JCLemme/eprisc-open-computer/software/rom/bios_main.v

rContents[0] = 32'h80000026;
rContents[1] = 32'h43F01FF0;
rContents[2] = 32'h61F00000;
rContents[3] = 32'hD000029E;
rContents[4] = 32'h63F01FF1;
rContents[5] = 32'h41F00000;
rContents[6] = 32'hF0000000;
rContents[7] = 32'hD00002BC;
rContents[8] = 32'h63F01FF1;
rContents[9] = 32'hF0000000;
rContents[10] = 32'h43F01FF2;
rContents[11] = 32'h61F00000;
rContents[12] = 32'h43F01FF3;
rContents[13] = 32'h61F00000;
rContents[14] = 32'hD00003E9;
rContents[15] = 32'h63F01FF4;
rContents[16] = 32'h41F00000;
rContents[17] = 32'h41F00000;
rContents[18] = 32'hF0000000;
rContents[19] = 32'h43F01FF2;
rContents[20] = 32'h61F00000;
rContents[21] = 32'h43F01FF3;
rContents[22] = 32'h61F00000;
rContents[23] = 32'hD0000415;
rContents[24] = 32'h63F01FF4;
rContents[25] = 32'h41F00000;
rContents[26] = 32'h41F00000;
rContents[27] = 32'hF0000000;
rContents[28] = 32'hD0000340;
rContents[29] = 32'h63F01FF5;
rContents[30] = 32'hF0000000;
rContents[31] = 32'h238000FF;
rContents[32] = 32'h3300FFFF;
rContents[33] = 32'h18133001;
rContents[34] = 32'h18E03000;
rContents[35] = 32'h820FFFFE;
rContents[36] = 32'h18422801;
rContents[37] = 32'h800FFFFA;
rContents[38] = 32'h21001100;
rContents[39] = 32'h23000000;
rContents[40] = 32'h800FFFF7;
rContents[41] = 32'hD00001CD;
rContents[42] = 32'h24007FFF;
rContents[43] = 32'h61400000;
rContents[44] = 32'h24000000;
rContents[45] = 32'h61400000;
rContents[46] = 32'hD00001D8;
rContents[47] = 32'h41400000;
rContents[48] = 32'h41400000;
rContents[49] = 32'h24000132;
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
rContents[283] = 32'h48500003;
rContents[284] = 32'h48600004;
rContents[285] = 32'h48700005;
rContents[286] = 32'h61700000;
rContents[287] = 32'h61500000;
rContents[288] = 32'hD000030C;
rContents[289] = 32'h41500000;
rContents[290] = 32'h41700000;
rContents[291] = 32'h18E0F000;
rContents[292] = 32'h82000009;
rContents[293] = 32'h18055001;
rContents[294] = 32'h18077080;
rContents[295] = 32'h18166001;
rContents[296] = 32'h18E06000;
rContents[297] = 32'h820FFFF5;
rContents[298] = 32'hD00003A4;
rContents[299] = 32'h48700005;
rContents[300] = 32'h80700000;
rContents[301] = 32'h240001EE;
rContents[302] = 32'h61400000;
rContents[303] = 32'hD00001FE;
rContents[304] = 32'h41400000;
rContents[305] = 32'h80000496;
rContents[306] = 32'h65705249;
rContents[307] = 32'h53432042;
rContents[308] = 32'h6F6F746C;
rContents[309] = 32'h6F616465;
rContents[310] = 32'h72207633;
rContents[311] = 32'h2E340A0D;
rContents[312] = 32'h636F7079;
rContents[313] = 32'h72696768;
rContents[314] = 32'h74203230;
rContents[315] = 32'h31352D32;
rContents[316] = 32'h30313720;
rContents[317] = 32'h50726F70;
rContents[318] = 32'h6F727469;
rContents[319] = 32'h6F6E616C;
rContents[320] = 32'h204C6162;
rContents[321] = 32'h730A0D0A;
rContents[322] = 32'h0D000000;
rContents[323] = 32'h41747465;
rContents[324] = 32'h6D707469;
rContents[325] = 32'h6E672074;
rContents[326] = 32'h6F206D6F;
rContents[327] = 32'h756E7420;
rContents[328] = 32'h53442063;
rContents[329] = 32'h61726420;
rContents[330] = 32'h696E2073;
rContents[331] = 32'h6C6F7420;
rContents[332] = 32'h412E2E2E;
rContents[333] = 32'h0A0D0000;
rContents[334] = 32'h41747465;
rContents[335] = 32'h6D707469;
rContents[336] = 32'h6E672074;
rContents[337] = 32'h6F206D6F;
rContents[338] = 32'h756E7420;
rContents[339] = 32'h53442063;
rContents[340] = 32'h61726420;
rContents[341] = 32'h696E2073;
rContents[342] = 32'h6C6F7420;
rContents[343] = 32'h422E2E2E;
rContents[344] = 32'h0A0D0000;
rContents[345] = 32'h20205344;
rContents[346] = 32'h20636172;
rContents[347] = 32'h64206D6F;
rContents[348] = 32'h756E7465;
rContents[349] = 32'h64207375;
rContents[350] = 32'h63636573;
rContents[351] = 32'h7366756C;
rContents[352] = 32'h6C792E0A;
rContents[353] = 32'h0D0A0D00;
rContents[354] = 32'h20204572;
rContents[355] = 32'h726F7220;
rContents[356] = 32'h6D6F756E;
rContents[357] = 32'h74696E67;
rContents[358] = 32'h20534420;
rContents[359] = 32'h63617264;
rContents[360] = 32'h2E0A0D0A;
rContents[361] = 32'h0D000000;
rContents[362] = 32'h46657463;
rContents[363] = 32'h68696E67;
rContents[364] = 32'h20646973;
rContents[365] = 32'h6B20696E;
rContents[366] = 32'h666F2E2E;
rContents[367] = 32'h2E0A0D00;
rContents[368] = 32'h20204469;
rContents[369] = 32'h736B2061;
rContents[370] = 32'h70706561;
rContents[371] = 32'h72732074;
rContents[372] = 32'h6F206265;
rContents[373] = 32'h20636F72;
rContents[374] = 32'h72757074;
rContents[375] = 32'h2E0A0D0A;
rContents[376] = 32'h0D000000;
rContents[377] = 32'h2020466F;
rContents[378] = 32'h756E6420;
rContents[379] = 32'h6469736B;
rContents[380] = 32'h20270000;
rContents[381] = 32'h27206174;
rContents[382] = 32'h20626C6F;
rContents[383] = 32'h636B2030;
rContents[384] = 32'h2E0A0D00;
rContents[385] = 32'h20204469;
rContents[386] = 32'h736B2061;
rContents[387] = 32'h70706561;
rContents[388] = 32'h72732074;
rContents[389] = 32'h6F206265;
rContents[390] = 32'h20656D70;
rContents[391] = 32'h74792E0A;
rContents[392] = 32'h0D0A0D00;
rContents[393] = 32'h2020466F;
rContents[394] = 32'h756E6420;
rContents[395] = 32'h00000000;
rContents[396] = 32'h20656E74;
rContents[397] = 32'h72696573;
rContents[398] = 32'h206F6E20;
rContents[399] = 32'h6469736B;
rContents[400] = 32'h2E0A0D0A;
rContents[401] = 32'h0D000000;
rContents[402] = 32'h41766169;
rContents[403] = 32'h6C61626C;
rContents[404] = 32'h6520656E;
rContents[405] = 32'h74726965;
rContents[406] = 32'h733A0A0D;
rContents[407] = 32'h00000000;
rContents[408] = 32'h3A20456E;
rContents[409] = 32'h74727920;
rContents[410] = 32'h27000000;
rContents[411] = 32'h273A2073;
rContents[412] = 32'h74617274;
rContents[413] = 32'h20000000;
rContents[414] = 32'h2C206C65;
rContents[415] = 32'h6E677468;
rContents[416] = 32'h20000000;
rContents[417] = 32'h2C206C6F;
rContents[418] = 32'h61642000;
rContents[419] = 32'h53656C65;
rContents[420] = 32'h63742061;
rContents[421] = 32'h6E20656E;
rContents[422] = 32'h74727920;
rContents[423] = 32'h746F2065;
rContents[424] = 32'h78656375;
rContents[425] = 32'h74652C20;
rContents[426] = 32'h6F722074;
rContents[427] = 32'h79706520;
rContents[428] = 32'h274D2720;
rContents[429] = 32'h746F2065;
rContents[430] = 32'h6E746572;
rContents[431] = 32'h20746865;
rContents[432] = 32'h206D6F6E;
rContents[433] = 32'h69746F72;
rContents[434] = 32'h3A200000;
rContents[435] = 32'h20204C6F;
rContents[436] = 32'h6164696E;
rContents[437] = 32'h6720656E;
rContents[438] = 32'h7472792E;
rContents[439] = 32'h2E2E0A0D;
rContents[440] = 32'h0A0D0000;
rContents[441] = 32'h53746172;
rContents[442] = 32'h74696E67;
rContents[443] = 32'h20504F53;
rContents[444] = 32'h54732E2E;
rContents[445] = 32'h2E0A0D00;
rContents[446] = 32'h20204D65;
rContents[447] = 32'h6D6F7279;
rContents[448] = 32'h20202020;
rContents[449] = 32'h20202020;
rContents[450] = 32'h20200000;
rContents[451] = 32'h20205541;
rContents[452] = 32'h52542020;
rContents[453] = 32'h20202020;
rContents[454] = 32'h20202020;
rContents[455] = 32'h20200000;
rContents[456] = 32'h20205350;
rContents[457] = 32'h49202020;
rContents[458] = 32'h20202020;
rContents[459] = 32'h20202020;
rContents[460] = 32'h20200000;
rContents[461] = 32'h20207379;
rContents[462] = 32'h73582042;
rContents[463] = 32'h75732020;
rContents[464] = 32'h20202020;
rContents[465] = 32'h20200000;
rContents[466] = 32'h2020492F;
rContents[467] = 32'h4F20436F;
rContents[468] = 32'h6E74726F;
rContents[469] = 32'h6C6C6572;
rContents[470] = 32'h20200000;
rContents[471] = 32'h4F4B0A0D;
rContents[472] = 32'h00000000;
rContents[473] = 32'h4641494C;
rContents[474] = 32'h0A0D0000;
rContents[475] = 32'h2020504F;
rContents[476] = 32'h53542073;
rContents[477] = 32'h75636365;
rContents[478] = 32'h73736675;
rContents[479] = 32'h6C2E0A0D;
rContents[480] = 32'h0A0D0000;
rContents[481] = 32'h2020504F;
rContents[482] = 32'h53542075;
rContents[483] = 32'h6E737563;
rContents[484] = 32'h63657373;
rContents[485] = 32'h66756C2E;
rContents[486] = 32'h0A0D0A0D;
rContents[487] = 32'h00000000;
rContents[488] = 32'h2020504F;
rContents[489] = 32'h53547320;
rContents[490] = 32'h636F6D70;
rContents[491] = 32'h6C657465;
rContents[492] = 32'h2E0A0D0A;
rContents[493] = 32'h0D000000;
rContents[494] = 32'h456E7465;
rContents[495] = 32'h72696E67;
rContents[496] = 32'h206D6F6E;
rContents[497] = 32'h69746F72;
rContents[498] = 32'h2E2E2E0A;
rContents[499] = 32'h0D0A0D00;
rContents[500] = 32'h0A0D0000;
rContents[501] = 32'h20200000;
rContents[502] = 32'h61C00000;
rContents[503] = 32'h2C002000;
rContents[504] = 32'h2F010001;
rContents[505] = 32'h6CF00000;
rContents[506] = 32'h04000000;
rContents[507] = 32'h04000000;
rContents[508] = 32'h04000000;
rContents[509] = 32'h04000000;
rContents[510] = 32'h4CF00000;
rContents[511] = 32'h18F0F001;
rContents[512] = 32'h820FFFFE;
rContents[513] = 32'h4CF00000;
rContents[514] = 32'h18F0F002;
rContents[515] = 32'h820FFFFE;
rContents[516] = 32'h41C00000;
rContents[517] = 32'hF0000000;
rContents[518] = 32'h61E00000;
rContents[519] = 32'h61D00000;
rContents[520] = 32'h61C00000;
rContents[521] = 32'h18111004;
rContents[522] = 32'h2C002000;
rContents[523] = 32'h41D00000;
rContents[524] = 32'h41E00000;
rContents[525] = 32'h18011006;
rContents[526] = 32'h2F600008;
rContents[527] = 32'h103FFE00;
rContents[528] = 32'h186FF010;
rContents[529] = 32'h103FFD00;
rContents[530] = 32'h6CF00001;
rContents[531] = 32'h2F010005;
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
rContents[859] = 32'hF0000000;
rContents[860] = 32'h61C00000;
rContents[861] = 32'h61D00000;
rContents[862] = 32'h61E00000;
rContents[863] = 32'h2C000000;
rContents[864] = 32'h61C00000;
rContents[865] = 32'hD00FFF2C;
rContents[866] = 32'h41C00000;
rContents[867] = 32'h2C00000B;
rContents[868] = 32'hD00FFF5F;
rContents[869] = 32'h181CC001;
rContents[870] = 32'h18E0C000;
rContents[871] = 32'h820FFFFD;
rContents[872] = 32'h2C000001;
rContents[873] = 32'h61C00000;
rContents[874] = 32'hD00FFF23;
rContents[875] = 32'h41C00000;
rContents[876] = 32'h2C000000;
rContents[877] = 32'h61C00000;
rContents[878] = 32'h2C000000;
rContents[879] = 32'h61C00000;
rContents[880] = 32'h2D000001;
rContents[881] = 32'h186DD000;
rContents[882] = 32'h2E000000;
rContents[883] = 32'hD0000084;
rContents[884] = 32'h10E0FD00;
rContents[885] = 32'h81000005;
rContents[886] = 32'h180EE001;
rContents[887] = 32'h18E0E402;
rContents[888] = 32'h8100006E;
rContents[889] = 32'h800FFFFA;
rContents[890] = 32'h41C00000;
rContents[891] = 32'h41C00000;
rContents[892] = 32'h2C000008;
rContents[893] = 32'h61C00000;
rContents[894] = 32'h2C0001AA;
rContents[895] = 32'h61C00000;
rContents[896] = 32'hD0000077;
rContents[897] = 32'h41C00000;
rContents[898] = 32'h41C00000;
rContents[899] = 32'h2D000001;
rContents[900] = 32'h186DD002;
rContents[901] = 32'h10F0FD00;
rContents[902] = 32'h8200000C;
rContents[903] = 32'hD00FFF3C;
rContents[904] = 32'hD00FFF3B;
rContents[905] = 32'hD00FFF3A;
rContents[906] = 32'h18F0F001;
rContents[907] = 32'h8100005D;
rContents[908] = 32'hD00FFF37;
rContents[909] = 32'h18E0F0AA;
rContents[910] = 32'h8200005A;
rContents[911] = 32'h2E000001;
rContents[912] = 32'h186EE001;
rContents[913] = 32'h80000014;
rContents[914] = 32'h2C000037;
rContents[915] = 32'h61C00000;
rContents[916] = 32'h2C000000;
rContents[917] = 32'h61C00000;
rContents[918] = 32'hD0000061;
rContents[919] = 32'h41C00000;
rContents[920] = 32'h41C00000;
rContents[921] = 32'h2C000029;
rContents[922] = 32'h61C00000;
rContents[923] = 32'h2C000000;
rContents[924] = 32'h61C00000;
rContents[925] = 32'hD000005A;
rContents[926] = 32'h41C00000;
rContents[927] = 32'h41C00000;
rContents[928] = 32'h2E000000;
rContents[929] = 32'h10E0FD00;
rContents[930] = 32'h82000003;
rContents[931] = 32'h2E000001;
rContents[932] = 32'h186EE000;
rContents[933] = 32'h2D000000;
rContents[934] = 32'h18F0E003;
rContents[935] = 32'h81000013;
rContents[936] = 32'h2C000037;
rContents[937] = 32'h61C00000;
rContents[938] = 32'h2C000000;
rContents[939] = 32'h61C00000;
rContents[940] = 32'hD000004B;
rContents[941] = 32'h41C00000;
rContents[942] = 32'h41C00000;
rContents[943] = 32'h2C000029;
rContents[944] = 32'h61C00000;
rContents[945] = 32'h2C000000;
rContents[946] = 32'h18F0E002;
rContents[947] = 32'h81000002;
rContents[948] = 32'h2C804000;
rContents[949] = 32'h61C00000;
rContents[950] = 32'hD0000041;
rContents[951] = 32'h41C00000;
rContents[952] = 32'h41C00000;
rContents[953] = 32'h80000008;
rContents[954] = 32'h2C000029;
rContents[955] = 32'h61C00000;
rContents[956] = 32'h2C000000;
rContents[957] = 32'h61C00000;
rContents[958] = 32'hD0000039;
rContents[959] = 32'h41C00000;
rContents[960] = 32'h41C00000;
rContents[961] = 32'h18F0F001;
rContents[962] = 32'h81000005;
rContents[963] = 32'h180DD001;
rContents[964] = 32'h18E0D480;
rContents[965] = 32'h81000023;
rContents[966] = 32'h800FFFE0;
rContents[967] = 32'h18F0E002;
rContents[968] = 32'h81000013;
rContents[969] = 32'h2C00003A;
rContents[970] = 32'h61C00000;
rContents[971] = 32'h2C000000;
rContents[972] = 32'h61C00000;
rContents[973] = 32'hD000002A;
rContents[974] = 32'h41C00000;
rContents[975] = 32'h41C00000;
rContents[976] = 32'h18E0F000;
rContents[977] = 32'h82000017;
rContents[978] = 32'hD00FFEF1;
rContents[979] = 32'h18F0F040;
rContents[980] = 32'h81000004;
rContents[981] = 32'h2C000001;
rContents[982] = 32'h186CC002;
rContents[983] = 32'h103EEC00;
rContents[984] = 32'hD00FFEEB;
rContents[985] = 32'hD00FFEEA;
rContents[986] = 32'hD00FFEE9;
rContents[987] = 32'h2C000010;
rContents[988] = 32'h61C00000;
rContents[989] = 32'h2C000200;
rContents[990] = 32'h61C00000;
rContents[991] = 32'hD0000018;
rContents[992] = 32'h41C00000;
rContents[993] = 32'h41C00000;
rContents[994] = 32'h18E0F000;
rContents[995] = 32'h82000005;
rContents[996] = 32'h8000000A;
rContents[997] = 32'hD00001B4;
rContents[998] = 32'h41C00000;
rContents[999] = 32'h41C00000;
rContents[1000] = 32'h2C000000;
rContents[1001] = 32'h61C00000;
rContents[1002] = 32'hD00FFEA3;
rContents[1003] = 32'h41C00000;
rContents[1004] = 32'h2F0000FF;
rContents[1005] = 32'h80000006;
rContents[1006] = 32'h2C000000;
rContents[1007] = 32'h61C00000;
rContents[1008] = 32'hD00FFE9D;
rContents[1009] = 32'h41C00000;
rContents[1010] = 32'h08FE0000;
rContents[1011] = 32'h41E00000;
rContents[1012] = 32'h41D00000;
rContents[1013] = 32'h41C00000;
rContents[1014] = 32'hF0000000;
rContents[1015] = 32'h61C00000;
rContents[1016] = 32'h61D00000;
rContents[1017] = 32'h18111003;
rContents[1018] = 32'h41D00000;
rContents[1019] = 32'h41C00000;
rContents[1020] = 32'h18011005;
rContents[1021] = 32'hD00FFEC6;
rContents[1022] = 32'h183CC040;
rContents[1023] = 32'h61C00000;
rContents[1024] = 32'hD00FFEA1;
rContents[1025] = 32'h41C00000;
rContents[1026] = 32'h61C00000;
rContents[1027] = 32'h08CD0000;
rContents[1028] = 32'h18DDCCFF;
rContents[1029] = 32'h61D00000;
rContents[1030] = 32'hD00FFE9B;
rContents[1031] = 32'h41D00000;
rContents[1032] = 32'h18DDC8FF;
rContents[1033] = 32'h61D00000;
rContents[1034] = 32'hD00FFE97;
rContents[1035] = 32'h41D00000;
rContents[1036] = 32'h18DDC4FF;
rContents[1037] = 32'h61D00000;
rContents[1038] = 32'hD00FFE93;
rContents[1039] = 32'h41D00000;
rContents[1040] = 32'h18DDC0FF;
rContents[1041] = 32'h61D00000;
rContents[1042] = 32'hD00FFE8F;
rContents[1043] = 32'h41D00000;
rContents[1044] = 32'h41C00000;
rContents[1045] = 32'h18E0C040;
rContents[1046] = 32'h82000003;
rContents[1047] = 32'h2D000095;
rContents[1048] = 32'h80000006;
rContents[1049] = 32'h18E0C048;
rContents[1050] = 32'h82000003;
rContents[1051] = 32'h2D000087;
rContents[1052] = 32'h80000002;
rContents[1053] = 32'h2D0000FF;
rContents[1054] = 32'h61D00000;
rContents[1055] = 32'hD00FFE82;
rContents[1056] = 32'h41D00000;
rContents[1057] = 32'h2D00000A;
rContents[1058] = 32'hD00FFEA1;
rContents[1059] = 32'h18E0F0FF;
rContents[1060] = 32'h82000005;
rContents[1061] = 32'h181DD001;
rContents[1062] = 32'h18E0D000;
rContents[1063] = 32'h81000002;
rContents[1064] = 32'h800FFFFA;
rContents[1065] = 32'h41D00000;
rContents[1066] = 32'h41C00000;
rContents[1067] = 32'hF0000000;
rContents[1068] = 32'h61C00000;
rContents[1069] = 32'h61D00000;
rContents[1070] = 32'h61E00000;
rContents[1071] = 32'h18111004;
rContents[1072] = 32'h41D00000;
rContents[1073] = 32'h41C00000;
rContents[1074] = 32'h18011006;
rContents[1075] = 32'h2F000001;
rContents[1076] = 32'h61F00000;
rContents[1077] = 32'hD00FFE58;
rContents[1078] = 32'h41F00000;
rContents[1079] = 32'h186DD009;
rContents[1080] = 32'h2F000011;
rContents[1081] = 32'h61F00000;
rContents[1082] = 32'h61D00000;
rContents[1083] = 32'hD00FFFBC;
rContents[1084] = 32'h18111002;
rContents[1085] = 32'h18E0F000;
rContents[1086] = 32'h82000023;
rContents[1087] = 32'hD00FFE84;
rContents[1088] = 32'h18E0F0FE;
rContents[1089] = 32'h820FFFFE;
rContents[1090] = 32'h2E000080;
rContents[1091] = 32'h2D000000;
rContents[1092] = 32'hD00FFE7F;
rContents[1093] = 32'h186DF018;
rContents[1094] = 32'hD00FFE7D;
rContents[1095] = 32'h186FF010;
rContents[1096] = 32'h103DDF00;
rContents[1097] = 32'hD00FFE7A;
rContents[1098] = 32'h186FF008;
rContents[1099] = 32'h103DDF00;
rContents[1100] = 32'hD00FFE77;
rContents[1101] = 32'h103DDF00;
rContents[1102] = 32'h6CD00000;
rContents[1103] = 32'h180CC001;
rContents[1104] = 32'h181EE001;
rContents[1105] = 32'h18E0E000;
rContents[1106] = 32'h820FFFF2;
rContents[1107] = 32'hD00FFE70;
rContents[1108] = 32'hD00FFE6F;
rContents[1109] = 32'h2F000000;
rContents[1110] = 32'h61F00000;
rContents[1111] = 32'hD00FFE36;
rContents[1112] = 32'h41F00000;
rContents[1113] = 32'hD00FFE6A;
rContents[1114] = 32'hD00FFE69;
rContents[1115] = 32'hD00FFE68;
rContents[1116] = 32'hD00FFE67;
rContents[1117] = 32'hD00FFE66;
rContents[1118] = 32'hD00FFE65;
rContents[1119] = 32'h2F000000;
rContents[1120] = 32'h80000009;
rContents[1121] = 32'h61F00000;
rContents[1122] = 32'hD00FFE7F;
rContents[1123] = 32'h41F00000;
rContents[1124] = 32'h2F000000;
rContents[1125] = 32'h61F00000;
rContents[1126] = 32'hD00FFE27;
rContents[1127] = 32'h41F00000;
rContents[1128] = 32'h2F0000FF;
rContents[1129] = 32'h41E00000;
rContents[1130] = 32'h41D00000;
rContents[1131] = 32'h41C00000;
rContents[1132] = 32'hF0000000;
rContents[1133] = 32'h61C00000;
rContents[1134] = 32'h61D00000;
rContents[1135] = 32'h61E00000;
rContents[1136] = 32'h18111004;
rContents[1137] = 32'h41D00000;
rContents[1138] = 32'h41C00000;
rContents[1139] = 32'h18011006;
rContents[1140] = 32'h2F000001;
rContents[1141] = 32'h61F00000;
rContents[1142] = 32'hD00FFE17;
rContents[1143] = 32'h41F00000;
rContents[1144] = 32'h2F000018;
rContents[1145] = 32'h61F00000;
rContents[1146] = 32'h61D00000;
rContents[1147] = 32'hD00FFF7C;
rContents[1148] = 32'h18111002;
rContents[1149] = 32'h18E0F000;
rContents[1150] = 32'h8200002E;
rContents[1151] = 32'h2F0000FE;
rContents[1152] = 32'h61F00000;
rContents[1153] = 32'hD00FFE20;
rContents[1154] = 32'h41F00000;
rContents[1155] = 32'h2E000080;
rContents[1156] = 32'h4CD00000;
rContents[1157] = 32'h61C00000;
rContents[1158] = 32'h182CDCFF;
rContents[1159] = 32'h188DD018;
rContents[1160] = 32'h61D00000;
rContents[1161] = 32'hD00FFE18;
rContents[1162] = 32'h41D00000;
rContents[1163] = 32'h182CD8FF;
rContents[1164] = 32'h188DD010;
rContents[1165] = 32'h61D00000;
rContents[1166] = 32'hD00FFE13;
rContents[1167] = 32'h41D00000;
rContents[1168] = 32'h182CD4FF;
rContents[1169] = 32'h188DD008;
rContents[1170] = 32'h61D00000;
rContents[1171] = 32'hD00FFE0E;
rContents[1172] = 32'h41D00000;
rContents[1173] = 32'h182CD0FF;
rContents[1174] = 32'h61D00000;
rContents[1175] = 32'hD00FFE0A;
rContents[1176] = 32'h41D00000;
rContents[1177] = 32'h41C00000;
rContents[1178] = 32'h180CC001;
rContents[1179] = 32'h181EE001;
rContents[1180] = 32'h18E0E000;
rContents[1181] = 32'h820FFFE7;
rContents[1182] = 32'h2F0000FF;
rContents[1183] = 32'h61F00000;
rContents[1184] = 32'hD00FFE01;
rContents[1185] = 32'hD00FFE00;
rContents[1186] = 32'h41F00000;
rContents[1187] = 32'hD00FFE20;
rContents[1188] = 32'h18E0F0FF;
rContents[1189] = 32'h820FFFFE;
rContents[1190] = 32'h2F000000;
rContents[1191] = 32'h61F00000;
rContents[1192] = 32'hD00FFDE5;
rContents[1193] = 32'h41F00000;
rContents[1194] = 32'h2F000000;
rContents[1195] = 32'h80000006;
rContents[1196] = 32'h2F000000;
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
rContents[1328] = 32'h41D00000;
rContents[1329] = 32'h41F00000;
rContents[1330] = 32'h18E0F028;
rContents[1331] = 32'h81000036;
rContents[1332] = 32'h80000036;
rContents[1333] = 32'h80000035;
rContents[1334] = 32'h183CC4FF;
rContents[1335] = 32'h2D000033;
rContents[1336] = 32'h61D00000;
rContents[1337] = 32'h61C00000;
rContents[1338] = 32'hD00FFCCC;
rContents[1339] = 32'h41C00000;
rContents[1340] = 32'h41D00000;
rContents[1341] = 32'h2D000031;
rContents[1342] = 32'h61D00000;
rContents[1343] = 32'hD00FFCE1;
rContents[1344] = 32'h41D00000;
rContents[1345] = 32'h180FF001;
rContents[1346] = 32'h61F00000;
rContents[1347] = 32'h2D000031;
rContents[1348] = 32'h61D00000;
rContents[1349] = 32'h61F00000;
rContents[1350] = 32'hD00FFCC0;
rContents[1351] = 32'h41F00000;
rContents[1352] = 32'h41D00000;
rContents[1353] = 32'h41F00000;
rContents[1354] = 32'h18E0F050;
rContents[1355] = 32'h8200001F;
rContents[1356] = 32'h2D000031;
rContents[1357] = 32'h61D00000;
rContents[1358] = 32'h2D000000;
rContents[1359] = 32'h61D00000;
rContents[1360] = 32'hD00FFCB6;
rContents[1361] = 32'h41D00000;
rContents[1362] = 32'h41D00000;
rContents[1363] = 32'h2D000032;
rContents[1364] = 32'h61D00000;
rContents[1365] = 32'hD00FFCCB;
rContents[1366] = 32'h41D00000;
rContents[1367] = 32'h180FF001;
rContents[1368] = 32'h61F00000;
rContents[1369] = 32'h2D000032;
rContents[1370] = 32'h61D00000;
rContents[1371] = 32'h61F00000;
rContents[1372] = 32'hD00FFCAA;
rContents[1373] = 32'h41F00000;
rContents[1374] = 32'h41D00000;
rContents[1375] = 32'h41F00000;
rContents[1376] = 32'h18E0F028;
rContents[1377] = 32'h82000009;
rContents[1378] = 32'h2D000032;
rContents[1379] = 32'h61D00000;
rContents[1380] = 32'h2D000000;
rContents[1381] = 32'h61D00000;
rContents[1382] = 32'hD00FFCA0;
rContents[1383] = 32'h41D00000;
rContents[1384] = 32'h41D00000;
rContents[1385] = 32'hD00FFF65;
rContents[1386] = 32'h41D00000;
rContents[1387] = 32'h41C00000;
rContents[1388] = 32'hF0000000;
rContents[1389] = 32'h0A0A416E;
rContents[1390] = 32'h20657272;
rContents[1391] = 32'h6F722068;
rContents[1392] = 32'h6173206F;
rContents[1393] = 32'h63637572;
rContents[1394] = 32'h65642E0A;
rContents[1395] = 32'h00000000;
rContents[1396] = 32'h0A0A4120;
rContents[1397] = 32'h66617461;
rContents[1398] = 32'h6C206572;
rContents[1399] = 32'h726F7220;
rContents[1400] = 32'h68617320;
rContents[1401] = 32'h6F636375;
rContents[1402] = 32'h7265642E;
rContents[1403] = 32'h0A000000;
rContents[1404] = 32'h43616C6C;
rContents[1405] = 32'h65642061;
rContents[1406] = 32'h74200000;
rContents[1407] = 32'h53746163;
rContents[1408] = 32'h6B747261;
rContents[1409] = 32'h63652028;
rContents[1410] = 32'h746F7020;
rContents[1411] = 32'h3136293A;
rContents[1412] = 32'h0A000000;
rContents[1413] = 32'h52656769;
rContents[1414] = 32'h73746572;
rContents[1415] = 32'h733A0A00;
rContents[1416] = 32'h52657375;
rContents[1417] = 32'h6D696E67;
rContents[1418] = 32'h2E0A0A00;
rContents[1419] = 32'h48616C74;
rContents[1420] = 32'h696E672E;
rContents[1421] = 32'h0A0A0000;
rContents[1422] = 32'h80000001;
rContents[1423] = 32'h2F000574;
rContents[1424] = 32'h61F00000;
rContents[1425] = 32'hD00FFD9C;
rContents[1426] = 32'h41F00000;
rContents[1427] = 32'h2F00057C;
rContents[1428] = 32'h61F00000;
rContents[1429] = 32'hD00FFD98;
rContents[1430] = 32'h41F00000;
rContents[1431] = 32'hD00FFD4A;
rContents[1432] = 32'h04200000;
rContents[1433] = 32'h61F00000;
rContents[1434] = 32'h2F00057C;
rContents[1435] = 32'h61F00000;
rContents[1436] = 32'hD00FFD91;
rContents[1437] = 32'h41F00000;
rContents[1438] = 32'h2F0000F0;
rContents[1439] = 32'h181FF001;
rContents[1440] = 32'h18E0F000;
rContents[1441] = 32'h820FFFFE;
rContents[1442] = 32'h18111001;
rContents[1443] = 32'hD00FFD3E;
rContents[1444] = 32'h18011001;
rContents[1445] = 32'h2F00000A;
rContents[1446] = 32'h61F00000;
rContents[1447] = 32'hD0000013;
rContents[1448] = 32'h41F00000;
rContents[1449] = 32'h2F00000D;
rContents[1450] = 32'h61F00000;
rContents[1451] = 32'hD000000F;
rContents[1452] = 32'h41F00000;
rContents[1453] = 32'h41F00000;
rContents[1454] = 32'hF0000000;
rContents[1455] = 32'hF0000000;
rContents[1456] = 32'hF0000000;
rContents[1457] = 32'h4C656D6F;
rContents[1458] = 32'h6E207630;
rContents[1459] = 32'h2E32202D;
rContents[1460] = 32'h20666F72;
rContents[1461] = 32'h20657052;
rContents[1462] = 32'h49534320;
rContents[1463] = 32'h76352073;
rContents[1464] = 32'h79737465;
rContents[1465] = 32'h6D730000;
rContents[1466] = 32'h18111001;
rContents[1467] = 32'h41F00000;
rContents[1468] = 32'h18011002;
rContents[1469] = 32'h61F00000;
rContents[1470] = 32'hD00FFC84;
rContents[1471] = 32'h41F00000;
rContents[1472] = 32'hF0000000;
rContents[1473] = 32'h800FFC81;
rContents[1474] = 32'h800FFF50;
rContents[1475] = 32'h800FFC9E;
rContents[1476] = 32'h800FFD1D;
rContents[1477] = 32'h800FFD68;
rContents[1478] = 32'h800FFFC9;
rContents[1479] = 32'h210017FF;
rContents[1480] = 32'h280005B1;
rContents[1481] = 32'h61800000;
rContents[1482] = 32'hD00FFFFB;
rContents[1483] = 32'h41800000;
rContents[1484] = 32'h26001000;
rContents[1485] = 32'h29000000;
rContents[1486] = 32'h2800000A;
rContents[1487] = 32'h61800000;
rContents[1488] = 32'hD00FFFEA;
rContents[1489] = 32'h41800000;
rContents[1490] = 32'h2800000D;
rContents[1491] = 32'h61800000;
rContents[1492] = 32'hD00FFFE6;
rContents[1493] = 32'h41800000;
rContents[1494] = 32'h2800003E;
rContents[1495] = 32'h61800000;
rContents[1496] = 32'hD00FFFE2;
rContents[1497] = 32'h41800000;
rContents[1498] = 32'hD00FFFE9;
rContents[1499] = 32'h18E0F008;
rContents[1500] = 32'h8200000E;
rContents[1501] = 32'h18E06000;
rContents[1502] = 32'h82000002;
rContents[1503] = 32'h800FFFFB;
rContents[1504] = 32'h18166002;
rContents[1505] = 32'h18199001;
rContents[1506] = 32'h46F00000;
rContents[1507] = 32'h61F00000;
rContents[1508] = 32'hD00FFFD6;
rContents[1509] = 32'h41F00000;
rContents[1510] = 32'h18066001;
rContents[1511] = 32'h2F000000;
rContents[1512] = 32'h66F00000;
rContents[1513] = 32'h800FFFF1;
rContents[1514] = 32'h18E0F00D;
rContents[1515] = 32'h82000003;
rContents[1516] = 32'h66F00000;
rContents[1517] = 32'h8000000A;
rContents[1518] = 32'h18F09180;
rContents[1519] = 32'h820FFFEB;
rContents[1520] = 32'h61F00000;
rContents[1521] = 32'hD00FFFC9;
rContents[1522] = 32'h41F00000;
rContents[1523] = 32'h66F00000;
rContents[1524] = 32'h18066001;
rContents[1525] = 32'h18099001;
rContents[1526] = 32'h800FFFE4;
rContents[1527] = 32'h26001000;
rContents[1528] = 32'h27000000;
rContents[1529] = 32'h46900000;
rContents[1530] = 32'h18E0900D;
rContents[1531] = 32'h82000005;
rContents[1532] = 32'h18E0703A;
rContents[1533] = 32'h82000002;
rContents[1534] = 32'h41800000;
rContents[1535] = 32'h800FFFCD;
rContents[1536] = 32'h18E09052;
rContents[1537] = 32'h8200000C;
rContents[1538] = 32'h2800000A;
rContents[1539] = 32'h61800000;
rContents[1540] = 32'hD00FFFB6;
rContents[1541] = 32'h41800000;
rContents[1542] = 32'h2800000D;
rContents[1543] = 32'h61800000;
rContents[1544] = 32'hD00FFFB2;
rContents[1545] = 32'h41800000;
rContents[1546] = 32'hD0400000;
rContents[1547] = 32'h18066001;
rContents[1548] = 32'h800FFFED;
rContents[1549] = 32'h18E0903A;
rContents[1550] = 32'h82000005;
rContents[1551] = 32'h2700003A;
rContents[1552] = 32'h61400000;
rContents[1553] = 32'h18066001;
rContents[1554] = 32'h800FFFE7;
rContents[1555] = 32'h18E0902E;
rContents[1556] = 32'h82000007;
rContents[1557] = 32'h18E0703A;
rContents[1558] = 32'h82000002;
rContents[1559] = 32'h41800000;
rContents[1560] = 32'h2700002E;
rContents[1561] = 32'h18066001;
rContents[1562] = 32'h800FFFDF;
rContents[1563] = 32'h18E09020;
rContents[1564] = 32'h82000003;
rContents[1565] = 32'h18066001;
rContents[1566] = 32'h800FFFDB;
rContents[1567] = 32'h25000000;
rContents[1568] = 32'h46900000;
rContents[1569] = 32'h18199030;
rContents[1570] = 32'h18E0900A;
rContents[1571] = 32'h84000007;
rContents[1572] = 32'h18199007;
rContents[1573] = 32'h18E0900A;
rContents[1574] = 32'h84000008;
rContents[1575] = 32'h18E09010;
rContents[1576] = 32'h84000002;
rContents[1577] = 32'h80000005;
rContents[1578] = 32'h18655004;
rContents[1579] = 32'h10355900;
rContents[1580] = 32'h18066001;
rContents[1581] = 32'h800FFFF3;
rContents[1582] = 32'h46900000;
rContents[1583] = 32'h18E0703A;
rContents[1584] = 32'h82000004;
rContents[1585] = 32'h64500000;
rContents[1586] = 32'h18044001;
rContents[1587] = 32'h800FFFC6;
rContents[1588] = 32'h61400000;
rContents[1589] = 32'h08450000;
rContents[1590] = 32'h18E0902E;
rContents[1591] = 32'h82000003;
rContents[1592] = 32'h41800000;
rContents[1593] = 32'h800FFFC0;
rContents[1594] = 32'h18E07000;
rContents[1595] = 32'h82000016;
rContents[1596] = 32'h41800000;
rContents[1597] = 32'h2800000A;
rContents[1598] = 32'h61800000;
rContents[1599] = 32'hD00FFF7B;
rContents[1600] = 32'h41800000;
rContents[1601] = 32'h2800000D;
rContents[1602] = 32'h61800000;
rContents[1603] = 32'hD00FFF77;
rContents[1604] = 32'h41800000;
rContents[1605] = 32'h61400000;
rContents[1606] = 32'hD00FFC9B;
rContents[1607] = 32'h41400000;
rContents[1608] = 32'h2800003A;
rContents[1609] = 32'h61800000;
rContents[1610] = 32'hD00FFF70;
rContents[1611] = 32'h41800000;
rContents[1612] = 32'h44800000;
rContents[1613] = 32'h61800000;
rContents[1614] = 32'hD00FFF76;
rContents[1615] = 32'h41800000;
rContents[1616] = 32'h800FFFA9;
rContents[1617] = 32'h18E0702E;
rContents[1618] = 32'hD20FFF74;
rContents[1619] = 32'h08840000;
rContents[1620] = 32'h41400000;
rContents[1621] = 32'h10E08400;
rContents[1622] = 32'h8B000002;
rContents[1623] = 32'h08840000;
rContents[1624] = 32'h101A8400;
rContents[1625] = 32'h180AA001;
rContents[1626] = 32'h61400000;
rContents[1627] = 32'h2800000A;
rContents[1628] = 32'h61800000;
rContents[1629] = 32'hD00FFF65;
rContents[1630] = 32'h41800000;
rContents[1631] = 32'h2800000A;
rContents[1632] = 32'h61800000;
rContents[1633] = 32'hD00FFF60;
rContents[1634] = 32'h41800000;
rContents[1635] = 32'h2800000D;
rContents[1636] = 32'h61800000;
rContents[1637] = 32'hD00FFF55;
rContents[1638] = 32'h41800000;
rContents[1639] = 32'h61400000;
rContents[1640] = 32'hD00FFC79;
rContents[1641] = 32'h41400000;
rContents[1642] = 32'h2800003A;
rContents[1643] = 32'h61800000;
rContents[1644] = 32'hD00FFF4E;
rContents[1645] = 32'h41800000;
rContents[1646] = 32'h18E0A008;
rContents[1647] = 32'h83000003;
rContents[1648] = 32'h08BA0000;
rContents[1649] = 32'h80000002;
rContents[1650] = 32'h2B000008;
rContents[1651] = 32'h101AAB00;
rContents[1652] = 32'h80000005;
rContents[1653] = 32'h28000020;
rContents[1654] = 32'h61800000;
rContents[1655] = 32'hD00FFF43;
rContents[1656] = 32'h41800000;
rContents[1657] = 32'h44800000;
rContents[1658] = 32'h61800000;
rContents[1659] = 32'hD00FFF49;
rContents[1660] = 32'h41800000;
rContents[1661] = 32'h18044001;
rContents[1662] = 32'h181BB001;
rContents[1663] = 32'h18E0B000;
rContents[1664] = 32'h820FFFF5;
rContents[1665] = 32'h18E0A000;
rContents[1666] = 32'h820FFFDD;
rContents[1667] = 32'h41400000;
rContents[1668] = 32'h27000000;
rContents[1669] = 32'h800FFF74;
