JCLemme/eprisc-open-computer/software/toolchain/flail/obj_dir/VepRISC_coreEmu_epRISC_machine.cpp

// Verilated -*- C++ -*-
// DESCRIPTION: Verilator output: Design implementation internals
// See VepRISC_coreEmu.h for the primary calling header

#include "VepRISC_coreEmu_epRISC_machine.h" // For This
#include "VepRISC_coreEmu__Syms.h"

#include "verilated_dpi.h"

//--------------------
// STATIC VARIABLES

VL_ST_SIG8(VepRISC_coreEmu_epRISC_machine::__Vtable1___PVT__core__DOT__rExec[512],0,0);

//--------------------

VL_CTOR_IMP(VepRISC_coreEmu_epRISC_machine) {
    VL_CELL (bus, VepRISC_coreEmu_epRISC_sysXMaster);
    // Reset internal values
    // Reset structure values
    _ctor_var_reset();
}

void VepRISC_coreEmu_epRISC_machine::__Vconfigure(VepRISC_coreEmu__Syms* vlSymsp, bool first) {
    if (0 && first) {}  // Prevent unused
    this->__VlSymsp = vlSymsp;
}

VepRISC_coreEmu_epRISC_machine::~VepRISC_coreEmu_epRISC_machine() {
}

//--------------------
// Internal Methods

void VepRISC_coreEmu_epRISC_machine::_settle__TOP__epRISC_coreEmu__machine__1(VepRISC_coreEmu__Syms* __restrict vlSymsp) {
    VL_DEBUG_IF(VL_PRINTF("        VepRISC_coreEmu_epRISC_machine::_settle__TOP__epRISC_coreEmu__machine__1\n"); );
    VepRISC_coreEmu* __restrict vlTOPp VL_ATTR_UNUSED = vlSymsp->TOPp;
    // Body
    vlSymsp->TOP__epRISC_coreEmu__machine__bus.iMasterClock 
	= vlSymsp->TOP__epRISC_coreEmu__machine.__PVT__wCoreBusMemClock;
}

VL_INLINE_OPT void VepRISC_coreEmu_epRISC_machine::_sequent__TOP__epRISC_coreEmu__machine__2(VepRISC_coreEmu__Syms* __restrict vlSymsp) {
    VL_DEBUG_IF(VL_PRINTF("        VepRISC_coreEmu_epRISC_machine::_sequent__TOP__epRISC_coreEmu__machine__2\n"); );
    VepRISC_coreEmu* __restrict vlTOPp VL_ATTR_UNUSED = vlSymsp->TOPp;
    // Body
    vlSymsp->TOP__epRISC_coreEmu__machine.__Vdly__clock__DOT__rClockSplit 
	= vlSymsp->TOP__epRISC_coreEmu__machine.__PVT__clock__DOT__rClockSplit;
    // ALWAYS at ../../../firmware/core/machine_v1r0.v:33
    vlSymsp->TOP__epRISC_coreEmu__machine.__Vdly__clock__DOT__rClockSplit 
	= (3U & ((IData)(1U) + (IData)(vlSymsp->TOP__epRISC_coreEmu__machine.__PVT__clock__DOT__rClockSplit)));
    if ((0U == (IData)(vlSymsp->TOP__epRISC_coreEmu__machine.__PVT__clock__DOT__rClockSplit))) {
	vlSymsp->TOP__epRISC_coreEmu__machine.__PVT__wCoreBusClock = 1U;
    }
    if ((1U == (IData)(vlSymsp->TOP__epRISC_coreEmu__machine.__PVT__clock__DOT__rClockSplit))) {
	vlSymsp->TOP__epRISC_coreEmu__machine.__PVT__wCoreBusMemClock = 1U;
    }
    if ((2U == (IData)(vlSymsp->TOP__epRISC_coreEmu__machine.__PVT__clock__DOT__rClockSplit))) {
	vlSymsp->TOP__epRISC_coreEmu__machine.__PVT__wCoreBusClock = 0U;
    }
    if ((3U == (IData)(vlSymsp->TOP__epRISC_coreEmu__machine.__PVT__clock__DOT__rClockSplit))) {
	vlSymsp->TOP__epRISC_coreEmu__machine.__PVT__wCoreBusMemClock = 0U;
    }
    vlSymsp->TOP__epRISC_coreEmu__machine.__PVT__clock__DOT__rClockSplit 
	= vlSymsp->TOP__epRISC_coreEmu__machine.__Vdly__clock__DOT__rClockSplit;
}

void VepRISC_coreEmu_epRISC_machine::_initial__TOP__epRISC_coreEmu__machine__3(VepRISC_coreEmu__Syms* __restrict vlSymsp) {
    VL_DEBUG_IF(VL_PRINTF("        VepRISC_coreEmu_epRISC_machine::_initial__TOP__epRISC_coreEmu__machine__3\n"); );
    VepRISC_coreEmu* __restrict vlTOPp VL_ATTR_UNUSED = vlSymsp->TOPp;
    // Body
    // INITIAL at ../../../firmware/core/machine_v1r0.v:29
    vlSymsp->TOP__epRISC_coreEmu__machine.__PVT__clock__DOT__rClockSplit = 0U;
}

VL_INLINE_OPT void VepRISC_coreEmu_epRISC_machine::_sequent__TOP__epRISC_coreEmu__machine__4(VepRISC_coreEmu__Syms* __restrict vlSymsp) {
    VL_DEBUG_IF(VL_PRINTF("        VepRISC_coreEmu_epRISC_machine::_sequent__TOP__epRISC_coreEmu__machine__4\n"); );
    VepRISC_coreEmu* __restrict vlTOPp VL_ATTR_UNUSED = vlSymsp->TOPp;
    // Body
    // ALWAYS at ../../../firmware/core/rom_v1r0.v:11
    vlSymsp->TOP__epRISC_coreEmu__machine.__PVT__tbrom__DOT__rDataOut 
	= vlSymsp->TOP__epRISC_coreEmu__machine.__PVT__tbrom__DOT__rContents
	[(0xfffU & vlSymsp->TOP__epRISC_coreEmu__machine.__PVT__wCoreBusAddress)];
    // ALWAYS at ../../../firmware/testbench/testmem_v1r0.v:13
    if (((IData)(vlSymsp->TOP__epRISC_coreEmu__machine.__PVT__wCoreBusWrite) 
	 & (IData)(vlSymsp->TOP__epRISC_coreEmu__machine.__PVT__wEnableRAM))) {
	vlSymsp->TOP__epRISC_coreEmu__machine.__PVT__tbram__DOT__rContents[(0xfffU 
									    & vlSymsp->TOP__epRISC_coreEmu__machine.__PVT__wCoreBusAddress)] 
	    = vlSymsp->TOP__epRISC_coreEmu__machine.__PVT__wCoreBusData;
    } else {
	vlSymsp->TOP__epRISC_coreEmu__machine.__PVT__tbram__DOT__rDataOut 
	    = vlSymsp->TOP__epRISC_coreEmu__machine.__PVT__tbram__DOT__rContents
	    [(0xfffU & vlSymsp->TOP__epRISC_coreEmu__machine.__PVT__wCoreBusAddress)];
    }
    // ALWAYS at ../../../firmware/testbench/testmem_v1r0.v:13
    if (((IData)(vlSymsp->TOP__epRISC_coreEmu__machine.__PVT__wCoreBusWrite) 
	 & (IData)(vlSymsp->TOP__epRISC_coreEmu__machine.__PVT__wEnableSDRAM))) {
	vlSymsp->TOP__epRISC_coreEmu__machine.__PVT__tbsdram__DOT__rContents[(0xfffU 
									      & vlSymsp->TOP__epRISC_coreEmu__machine.__PVT__wCoreBusAddress)] 
	    = vlSymsp->TOP__epRISC_coreEmu__machine.__PVT__wCoreBusData;
    } else {
	vlSymsp->TOP__epRISC_coreEmu__machine.__PVT__tbsdram__DOT__rDataOut 
	    = vlSymsp->TOP__epRISC_coreEmu__machine.__PVT__tbsdram__DOT__rContents
	    [(0xfffU & vlSymsp->TOP__epRISC_coreEmu__machine.__PVT__wCoreBusAddress)];
    }
}

VL_INLINE_OPT void VepRISC_coreEmu_epRISC_machine::_sequent__TOP__epRISC_coreEmu__machine__5(VepRISC_coreEmu__Syms* __restrict vlSymsp) {
    VL_DEBUG_IF(VL_PRINTF("        VepRISC_coreEmu_epRISC_machine::_sequent__TOP__epRISC_coreEmu__machine__5\n"); );
    VepRISC_coreEmu* __restrict vlTOPp VL_ATTR_UNUSED = vlSymsp->TOPp;
    // Body
    vlSymsp->TOP__epRISC_coreEmu__machine.__Vdlyvset__core__DOT__registers__DOT__rContents__v0 = 0U;
    vlSymsp->TOP__epRISC_coreEmu__machine.__Vdlyvset__core__DOT__registers__DOT__rContents__v1 = 0U;
    vlSymsp->TOP__epRISC_coreEmu__machine.__Vdly__core__DOT__rPipeState 
	= vlSymsp->TOP__epRISC_coreEmu__machine.__PVT__core__DOT__rPipeState;
    // ALWAYS at ../../../firmware/core/core_v5r0.v:63
    if ((1U & (~ (IData)(vlSymsp->TOP__epRISC_coreEmu__machine.__PVT__core__DOT__wBusOutWriteB)))) {
	vlSymsp->TOP__epRISC_coreEmu__machine.__PVT__core__DOT__wBusRegB 
	    = vlSymsp->TOP__epRISC_coreEmu__machine.__PVT__core__DOT__registers__DOT__rContents
	    [vlSymsp->TOP__epRISC_coreEmu__machine.core__DOT____Vcellinp__registers____pinNumber2];
    }
    // ALWAYS at ../../../firmware/core/core_v5r0.v:47
    if (vlSymsp->TOP__epRISC_coreEmu__machine.__PVT__core__DOT__wBusOutWriteA) {
	vlSymsp->TOP__epRISC_coreEmu__machine.__Vdlyvval__core__DOT__registers__DOT__rContents__v0 
	    = vlSymsp->TOP__epRISC_coreEmu__machine.__PVT__core__DOT__wBusOutA;
	vlSymsp->TOP__epRISC_coreEmu__machine.__Vdlyvset__core__DOT__registers__DOT__rContents__v0 = 1U;
	vlSymsp->TOP__epRISC_coreEmu__machine.__Vdlyvdim0__core__DOT__registers__DOT__rContents__v0 
	    = vlSymsp->TOP__epRISC_coreEmu__machine.core__DOT____Vcellinp__registers____pinNumber1;
    }
    if (vlSymsp->TOP__epRISC_coreEmu__machine.__PVT__core__DOT__wBusOutWriteB) {
	vlSymsp->TOP__epRISC_coreEmu__machine.__Vdlyvval__core__DOT__registers__DOT__rContents__v1 
	    = vlSymsp->TOP__epRISC_coreEmu__machine.__PVT__core__DOT__wBusOutB;
	vlSymsp->TOP__epRISC_coreEmu__machine.__Vdlyvset__core__DOT__registers__DOT__rContents__v1 = 1U;
	vlSymsp->TOP__epRISC_coreEmu__machine.__Vdlyvdim0__core__DOT__registers__DOT__rContents__v1 
	    = vlSymsp->TOP__epRISC_coreEmu__machine.core__DOT____Vcellinp__registers____pinNumber2;
    }
    // ALWAYS at ../../../firmware/core/core_v5r0.v:225
    if (vlTOPp->iBoardReset) {
	vlSymsp->TOP__epRISC_coreEmu__machine.__PVT__core__DOT__rPipePrevState 
	    = vlSymsp->TOP__epRISC_coreEmu__machine.__PVT__core__DOT__rPipeState;
	vlSymsp->TOP__epRISC_coreEmu__machine.__Vdly__core__DOT__rPipeState 
	    = vlSymsp->TOP__epRISC_coreEmu__machine.__PVT__core__DOT__rPipeNextState;
    } else {
	vlSymsp->TOP__epRISC_coreEmu__machine.__Vdly__core__DOT__rPipeState = 0U;
	vlSymsp->TOP__epRISC_coreEmu__machine.__PVT__core__DOT__rPipePrevState = 0U;
    }
}

VL_INLINE_OPT void VepRISC_coreEmu_epRISC_machine::_sequent__TOP__epRISC_coreEmu__machine__6(VepRISC_coreEmu__Syms* __restrict vlSymsp) {
    VL_DEBUG_IF(VL_PRINTF("        VepRISC_coreEmu_epRISC_machine::_sequent__TOP__epRISC_coreEmu__machine__6\n"); );
    VepRISC_coreEmu* __restrict vlTOPp VL_ATTR_UNUSED = vlSymsp->TOPp;
    // Variables
    VL_SIGW(__Vtemp1,95,0,3);
    //char	__VpadToAlign116[4];
    VL_SIGW(__Vtemp2,95,0,3);
    // Body
    vlSymsp->TOP__epRISC_coreEmu__machine.__Vdly__core__DOT__rRegInterruptStack[0U] 
	= vlSymsp->TOP__epRISC_coreEmu__machine.__PVT__core__DOT__rRegInterruptStack[0U];
    vlSymsp->TOP__epRISC_coreEmu__machine.__Vdly__core__DOT__rRegInterruptStack[1U] 
	= vlSymsp->TOP__epRISC_coreEmu__machine.__PVT__core__DOT__rRegInterruptStack[1U];
    vlSymsp->TOP__epRISC_coreEmu__machine.__Vdly__core__DOT__rRegInterruptStack[2U] 
	= vlSymsp->TOP__epRISC_coreEmu__machine.__PVT__core__DOT__rRegInterruptStack[2U];
    vlSymsp->TOP__epRISC_coreEmu__machine.__Vdly__core__DOT__rRegSP 
	= vlSymsp->TOP__epRISC_coreEmu__machine.__PVT__core__DOT__rRegSP;
    vlSymsp->TOP__epRISC_coreEmu__machine.__Vdly__core__DOT__rRegIP 
	= vlSymsp->TOP__epRISC_coreEmu__machine.__PVT__core__DOT__rRegIP;
    vlSymsp->TOP__epRISC_coreEmu__machine.__Vdly__core__DOT__rRegCS 
	= vlSymsp->TOP__epRISC_coreEmu__machine.__PVT__core__DOT__rRegCS;
    // ALWAYS at ../../../firmware/core/core_v5r0.v:485
    if (vlTOPp->iBoardReset) {
	if ((8U == (IData)(vlSymsp->TOP__epRISC_coreEmu__machine.__PVT__core__DOT__rPipeState))) {
	    VL_SHIFTR_WWI(96,96,32, __Vtemp1, vlSymsp->TOP__epRISC_coreEmu__machine.__PVT__core__DOT__rRegInterruptStack, 0x20U);
	    vlSymsp->TOP__epRISC_coreEmu__machine.__Vdly__core__DOT__rRegInterruptStack[0U] 
		= __Vtemp1[0U];
	    vlSymsp->TOP__epRISC_coreEmu__machine.__Vdly__core__DOT__rRegInterruptStack[1U] 
		= __Vtemp1[1U];
	    vlSymsp->TOP__epRISC_coreEmu__machine.__Vdly__core__DOT__rRegInterruptStack[2U] 
		= __Vtemp1[2U];
	    vlSymsp->TOP__epRISC_coreEmu__machine.__Vdly__core__DOT__rRegInterruptStack[2U] 
		= vlSymsp->TOP__epRISC_coreEmu__machine.__PVT__core__DOT__rRegIP;
	} else {
	    if (((5U == (IData)(vlSymsp->TOP__epRISC_coreEmu__machine.__PVT__core__DOT__rPipeState)) 
		 & (IData)(vlSymsp->TOP__epRISC_coreEmu__machine.__PVT__core__DOT__mBranchInterrupt))) {
		VL_SHIFTL_WWI(96,96,32, __Vtemp2, vlSymsp->TOP__epRISC_coreEmu__machine.__PVT__core__DOT__rRegInterruptStack, 0x20U);
		vlSymsp->TOP__epRISC_coreEmu__machine.__Vdly__core__DOT__rRegInterruptStack[0U] 
		    = __Vtemp2[0U];
		vlSymsp->TOP__epRISC_coreEmu__machine.__Vdly__core__DOT__rRegInterruptStack[1U] 
		    = __Vtemp2[1U];
		vlSymsp->TOP__epRISC_coreEmu__machine.__Vdly__core__DOT__rRegInterruptStack[2U] 
		    = __Vtemp2[2U];
	    }
	}
    } else {
	vlSymsp->TOP__epRISC_coreEmu__machine.__Vdly__core__DOT__rRegInterruptStack[0U] = 0U;
	vlSymsp->TOP__epRISC_coreEmu__machine.__Vdly__core__DOT__rRegInterruptStack[1U] = 0U;
	vlSymsp->TOP__epRISC_coreEmu__machine.__Vdly__core__DOT__rRegInterruptStack[2U] = 0U;
    }
    // ALWAYS at ../../../firmware/core/core_v5r0.v:290
    if (vlTOPp->iBoardReset) {
	if ((5U == (IData)(vlSymsp->TOP__epRISC_coreEmu__machine.__PVT__core__DOT__rPipeState))) {
	    if (((IData)(vlSymsp->TOP__epRISC_coreEmu__machine.__PVT__core__DOT__mBranchSaveStack) 
		 | ((~ (vlSymsp->TOP__epRISC_coreEmu__machine.__PVT__core__DOT__rRegCS 
			>> 7U)) & ((IData)(vlSymsp->TOP__epRISC_coreEmu__machine.__PVT__core__DOT__mBranchSaveStack) 
				   | ((IData)(vlSymsp->TOP__epRISC_coreEmu__machine.__PVT__core__DOT__mLoadStore) 
				      & (1U == (0xfU 
						& (vlSymsp->TOP__epRISC_coreEmu__machine.__PVT__core__DOT__rInst 
						   >> 0x18U)))))))) {
		vlSymsp->TOP__epRISC_coreEmu__machine.__Vdly__core__DOT__rRegSP 
		    = ((IData)(1U) + vlSymsp->TOP__epRISC_coreEmu__machine.__PVT__core__DOT__rRegSP);
	    } else {
		if (((IData)(vlSymsp->TOP__epRISC_coreEmu__machine.__PVT__core__DOT__mBranchLoadStack) 
		     | ((~ (vlSymsp->TOP__epRISC_coreEmu__machine.__PVT__core__DOT__rRegCS 
			    >> 7U)) & ((IData)(vlSymsp->TOP__epRISC_coreEmu__machine.__PVT__core__DOT__mBranchLoadStack) 
				       | ((IData)(vlSymsp->TOP__epRISC_coreEmu__machine.__PVT__core__DOT__mLoadLoad) 
					  & (1U == 
					     (0xfU 
					      & (vlSymsp->TOP__epRISC_coreEmu__machine.__PVT__core__DOT__rInst 
						 >> 0x18U)))))))) {
		    vlSymsp->TOP__epRISC_coreEmu__machine.__Vdly__core__DOT__rRegSP 
			= (vlSymsp->TOP__epRISC_coreEmu__machine.__PVT__core__DOT__rRegSP 
			   - (IData)(1U));
		} else {
		    if ((((~ (vlSymsp->TOP__epRISC_coreEmu__machine.__PVT__core__DOT__rRegCS 
			      >> 7U)) & (1U == (IData)(vlSymsp->TOP__epRISC_coreEmu__machine.__PVT__core__DOT__wBusOutAddrA))) 
			 & (IData)(vlSymsp->TOP__epRISC_coreEmu__machine.__PVT__core__DOT__wBusOutWriteA))) {
			vlSymsp->TOP__epRISC_coreEmu__machine.__Vdly__core__DOT__rRegSP 
			    = vlSymsp->TOP__epRISC_coreEmu__machine.__PVT__core__DOT__wBusOutA;
		    } else {
			if ((((~ (vlSymsp->TOP__epRISC_coreEmu__machine.__PVT__core__DOT__rRegCS 
				  >> 7U)) & (1U == (IData)(vlSymsp->TOP__epRISC_coreEmu__machine.__PVT__core__DOT__wBusOutAddrB))) 
			     & (IData)(vlSymsp->TOP__epRISC_coreEmu__machine.__PVT__core__DOT__wBusOutWriteB))) {
			    vlSymsp->TOP__epRISC_coreEmu__machine.__Vdly__core__DOT__rRegSP 
				= vlSymsp->TOP__epRISC_coreEmu__machine.__PVT__core__DOT__wBusOutB;
			}
		    }
		}
	    }
	}
    } else {
	vlSymsp->TOP__epRISC_coreEmu__machine.__Vdly__core__DOT__rRegSP = 0U;
    }
    // ALWAYS at ../../../firmware/core/core_v5r0.v:260
    if (vlTOPp->iBoardReset) {
	if ((5U == (IData)(vlSymsp->TOP__epRISC_coreEmu__machine.__PVT__core__DOT__rPipeState))) {
	    vlSymsp->TOP__epRISC_coreEmu__machine.__Vdly__core__DOT__rRegIP 
		= ((0x80000000U & vlSymsp->TOP__epRISC_coreEmu__machine.__PVT__core__DOT__rInst)
		    ? ((IData)(vlSymsp->TOP__epRISC_coreEmu__machine.__PVT__core__DOT__mBranchLoadStack)
		        ? ((IData)(1U) + vlSymsp->TOP__epRISC_coreEmu__machine.__PVT__core__DOT__rRegM)
		        : ((IData)(vlSymsp->TOP__epRISC_coreEmu__machine.__PVT__core__DOT__mBranchInterrupt)
			    ? ((IData)(1U) + vlSymsp->TOP__epRISC_coreEmu__machine.__PVT__core__DOT__rRegInterruptStack[2U])
			    : (IData)(vlSymsp->TOP__epRISC_coreEmu__machine.__PVT__core__DOT__rRegR)))
		    : ((((1U == (0x3fU & (vlSymsp->TOP__epRISC_coreEmu__machine.__PVT__core__DOT__rInst 
					  >> 0x1aU))) 
			 & (1U == (0x3fU & (vlSymsp->TOP__epRISC_coreEmu__machine.__PVT__core__DOT__rInst 
					    >> 0x14U)))) 
			& (vlSymsp->TOP__epRISC_coreEmu__machine.__PVT__core__DOT__rRegCS 
			   >> 6U)) ? (vlSymsp->TOP__epRISC_coreEmu__machine.__PVT__core__DOT__rRegInterruptBase 
				      + (0xfffffU & vlSymsp->TOP__epRISC_coreEmu__machine.__PVT__core__DOT__rInst))
		        : ((IData)(1U) + vlSymsp->TOP__epRISC_coreEmu__machine.__PVT__core__DOT__rRegIP)));
	} else {
	    if ((7U == (IData)(vlSymsp->TOP__epRISC_coreEmu__machine.__PVT__core__DOT__rPipeState))) {
		vlSymsp->TOP__epRISC_coreEmu__machine.__Vdly__core__DOT__rRegIP 
		    = ((((1U == (0x3fU & (vlSymsp->TOP__epRISC_coreEmu__machine.__PVT__core__DOT__rInst 
					  >> 0x1aU))) 
			 & (1U == (0x3fU & (vlSymsp->TOP__epRISC_coreEmu__machine.__PVT__core__DOT__rInst 
					    >> 0x14U)))) 
			& (vlSymsp->TOP__epRISC_coreEmu__machine.__PVT__core__DOT__rRegCS 
			   >> 6U)) ? (vlSymsp->TOP__epRISC_coreEmu__machine.__PVT__core__DOT__rRegInterruptBase 
				      + (0xfffffU & vlSymsp->TOP__epRISC_coreEmu__machine.__PVT__core__DOT__rInst))
		        : ((IData)(1U) + vlSymsp->TOP__epRISC_coreEmu__machine.__PVT__core__DOT__rRegIP));
	    } else {
		if ((8U == (IData)(vlSymsp->TOP__epRISC_coreEmu__machine.__PVT__core__DOT__rPipeState))) {
		    vlSymsp->TOP__epRISC_coreEmu__machine.__Vdly__core__DOT__rRegIP 
			= vlSymsp->TOP__epRISC_coreEmu__machine.__PVT__core__DOT__rRegInterruptBase;
		}
	    }
	}
    } else {
	vlSymsp->TOP__epRISC_coreEmu__machine.__Vdly__core__DOT__rRegIP = 0U;
    }
    // ALWAYS at ../../../firmware/core/core_v5r0.v:309
    if (vlTOPp->iBoardReset) {
	if ((5U == (IData)(vlSymsp->TOP__epRISC_coreEmu__machine.__PVT__core__DOT__rPipeState))) {
	    if (vlSymsp->TOP__epRISC_coreEmu__machine.__PVT__core__DOT__fCSFlagSet) {
		vlSymsp->TOP__epRISC_coreEmu__machine.__Vdly__core__DOT__rRegCS 
		    = ((0xfffffff7U & vlSymsp->TOP__epRISC_coreEmu__machine.__Vdly__core__DOT__rRegCS) 
		       | (8U & (((0U == (0x1fU & (vlSymsp->TOP__epRISC_coreEmu__machine.__PVT__core__DOT__rInst 
						  >> 0x14U)))
				  ? (IData)((vlSymsp->TOP__epRISC_coreEmu__machine.__PVT__core__DOT__rRegR 
					     >> 0x20U))
				  : (((1U == (0x1fU 
					      & (vlSymsp->TOP__epRISC_coreEmu__machine.__PVT__core__DOT__rInst 
						 >> 0x14U))) 
				      | (0xeU == (0x1fU 
						  & (vlSymsp->TOP__epRISC_coreEmu__machine.__PVT__core__DOT__rInst 
						     >> 0x14U)))) 
				     & (~ (IData)((vlSymsp->TOP__epRISC_coreEmu__machine.__PVT__core__DOT__rRegR 
						   >> 0x20U))))) 
				<< 3U)));
		vlSymsp->TOP__epRISC_coreEmu__machine.__Vdly__core__DOT__rRegCS 
		    = ((0xfffffffbU & vlSymsp->TOP__epRISC_coreEmu__machine.__Vdly__core__DOT__rRegCS) 
		       | ((VL_ULL(0) == vlSymsp->TOP__epRISC_coreEmu__machine.__PVT__core__DOT__rRegR) 
			  << 2U));
		vlSymsp->TOP__epRISC_coreEmu__machine.__Vdly__core__DOT__rRegCS 
		    = ((0xfffffffdU & vlSymsp->TOP__epRISC_coreEmu__machine.__Vdly__core__DOT__rRegCS) 
		       | (2U & ((IData)((vlSymsp->TOP__epRISC_coreEmu__machine.__PVT__core__DOT__rRegR 
					 >> 0x1fU)) 
				<< 1U)));
		vlSymsp->TOP__epRISC_coreEmu__machine.__Vdly__core__DOT__rRegCS 
		    = ((0xfffffffeU & vlSymsp->TOP__epRISC_coreEmu__machine.__Vdly__core__DOT__rRegCS) 
		       | (((0U == (0x1fU & (vlSymsp->TOP__epRISC_coreEmu__machine.__PVT__core__DOT__rInst 
					    >> 0x14U))) 
			   & ((((vlSymsp->TOP__epRISC_coreEmu__machine.__PVT__core__DOT__rRegA 
				 & vlSymsp->TOP__epRISC_coreEmu__machine.__PVT__core__DOT__rRegB) 
				>> 0x1fU) & (~ (IData)(
						       (vlSymsp->TOP__epRISC_coreEmu__machine.__PVT__core__DOT__rRegR 
							>> 0x1fU)))) 
			      | (((~ (vlSymsp->TOP__epRISC_coreEmu__machine.__PVT__core__DOT__rRegA 
				      >> 0x1fU)) & 
				  (~ (vlSymsp->TOP__epRISC_coreEmu__machine.__PVT__core__DOT__rRegB 
				      >> 0x1fU))) & (IData)(
							    (vlSymsp->TOP__epRISC_coreEmu__machine.__PVT__core__DOT__rRegR 
							     >> 0x1fU))))) 
			  | ((1U == (0x1fU & (vlSymsp->TOP__epRISC_coreEmu__machine.__PVT__core__DOT__rInst 
					      >> 0x14U))) 
			     & ((((~ (vlSymsp->TOP__epRISC_coreEmu__machine.__PVT__core__DOT__rRegA 
				      >> 0x1fU)) & 
				  (vlSymsp->TOP__epRISC_coreEmu__machine.__PVT__core__DOT__rRegB 
				   >> 0x1fU)) & (~ (IData)(
							   (vlSymsp->TOP__epRISC_coreEmu__machine.__PVT__core__DOT__rRegR 
							    >> 0x1fU)))) 
				| (((vlSymsp->TOP__epRISC_coreEmu__machine.__PVT__core__DOT__rRegA 
				     >> 0x1fU) & (~ 
						  (vlSymsp->TOP__epRISC_coreEmu__machine.__PVT__core__DOT__rRegB 
						   >> 0x1fU))) 
				   & (IData)((vlSymsp->TOP__epRISC_coreEmu__machine.__PVT__core__DOT__rRegR 
					      >> 0x1fU)))))));
	    }
	    if (((1U == (0x3fU & (vlSymsp->TOP__epRISC_coreEmu__machine.__PVT__core__DOT__rInst 
				  >> 0x1aU))) & (3U 
						 == 
						 (0x3fU 
						  & (vlSymsp->TOP__epRISC_coreEmu__machine.__PVT__core__DOT__rInst 
						     >> 0x14U))))) {
		vlSymsp->TOP__epRISC_coreEmu__machine.__Vdly__core__DOT__rRegCS 
		    = ((0xffff0fffU & vlSymsp->TOP__epRISC_coreEmu__machine.__Vdly__core__DOT__rRegCS) 
		       | (0xf000U & (vlSymsp->TOP__epRISC_coreEmu__machine.__PVT__core__DOT__rInst 
				     >> 4U)));
		vlSymsp->TOP__epRISC_coreEmu__machine.__Vdly__core__DOT__rRegCS 
		    = ((0xffffff7fU & vlSymsp->TOP__epRISC_coreEmu__machine.__Vdly__core__DOT__rRegCS) 
		       | (0x80U & (vlSymsp->TOP__epRISC_coreEmu__machine.__PVT__core__DOT__rInst 
				   >> 8U)));
	    }
	    if (vlSymsp->TOP__epRISC_coreEmu__machine.__PVT__core__DOT__mBranchInterrupt) {
		vlSymsp->TOP__epRISC_coreEmu__machine.__Vdly__core__DOT__rRegCS 
		    = (0x40U | vlSymsp->TOP__epRISC_coreEmu__machine.__Vdly__core__DOT__rRegCS);
	    }
	    if ((((~ (IData)(vlSymsp->TOP__epRISC_coreEmu__machine.__PVT__core__DOT__fCSHideRegs)) 
		  & (2U == (IData)(vlSymsp->TOP__epRISC_coreEmu__machine.__PVT__core__DOT__wBusOutAddrA))) 
		 & (IData)(vlSymsp->TOP__epRISC_coreEmu__machine.__PVT__core__DOT__wBusOutWriteA))) {
		vlSymsp->TOP__epRISC_coreEmu__machine.__Vdly__core__DOT__rRegCS 
		    = vlSymsp->TOP__epRISC_coreEmu__machine.__PVT__core__DOT__wBusOutA;
	    } else {
		if ((((~ (IData)(vlSymsp->TOP__epRISC_coreEmu__machine.__PVT__core__DOT__fCSHideRegs)) 
		      & (2U == (IData)(vlSymsp->TOP__epRISC_coreEmu__machine.__PVT__core__DOT__wBusOutAddrB))) 
		     & (IData)(vlSymsp->TOP__epRISC_coreEmu__machine.__PVT__core__DOT__wBusOutWriteB))) {
		    vlSymsp->TOP__epRISC_coreEmu__machine.__Vdly__core__DOT__rRegCS 
			= vlSymsp->TOP__epRISC_coreEmu__machine.__PVT__core__DOT__wBusOutB;
		}
	    }
	} else {
	    if ((8U == (IData)(vlSymsp->TOP__epRISC_coreEmu__machine.__PVT__core__DOT__rPipeState))) {
		vlSymsp->TOP__epRISC_coreEmu__machine.__Vdly__core__DOT__rRegCS 
		    = (0xffffffbfU & vlSymsp->TOP__epRISC_coreEmu__machine.__Vdly__core__DOT__rRegCS);
	    }
	}
    } else {
	vlSymsp->TOP__epRISC_coreEmu__machine.__Vdly__core__DOT__rRegCS = 0U;
    }
    vlSymsp->TOP__epRISC_coreEmu__machine.__PVT__core__DOT__rRegInterruptStack[0U] 
	= vlSymsp->TOP__epRISC_coreEmu__machine.__Vdly__core__DOT__rRegInterruptStack[0U];
    vlSymsp->TOP__epRISC_coreEmu__machine.__PVT__core__DOT__rRegInterruptStack[1U] 
	= vlSymsp->TOP__epRISC_coreEmu__machine.__Vdly__core__DOT__rRegInterruptStack[1U];
    vlSymsp->TOP__epRISC_coreEmu__machine.__PVT__core__DOT__rRegInterruptStack[2U] 
	= vlSymsp->TOP__epRISC_coreEmu__machine.__Vdly__core__DOT__rRegInterruptStack[2U];
    // ALWAYS at ../../../firmware/core/core_v5r0.v:387
    if (vlTOPp->iBoardReset) {
	if ((2U == (IData)(vlSymsp->TOP__epRISC_coreEmu__machine.__PVT__core__DOT__rPipeState))) {
	    vlSymsp->TOP__epRISC_coreEmu__machine.__PVT__core__DOT__rRegM 
		= ((0x80000000U & vlSymsp->TOP__epRISC_coreEmu__machine.__PVT__core__DOT__rInst)
		    ? vlSymsp->TOP__epRISC_coreEmu__machine.__PVT__core__DOT__rRegIP
		    : vlSymsp->TOP__epRISC_coreEmu__machine.__PVT__core__DOT__wBusInB);
	} else {
	    if (((4U == (IData)(vlSymsp->TOP__epRISC_coreEmu__machine.__PVT__core__DOT__rPipeState)) 
		 & ((IData)(vlSymsp->TOP__epRISC_coreEmu__machine.__PVT__core__DOT__mLoadLoad) 
		    | (IData)(vlSymsp->TOP__epRISC_coreEmu__machine.__PVT__core__DOT__mBranchLoadStack)))) {
		vlSymsp->TOP__epRISC_coreEmu__machine.__PVT__core__DOT__rRegM 
		    = vlSymsp->TOP__epRISC_coreEmu__machine.__PVT__wCoreBusData;
	    }
	}
    } else {
	vlSymsp->TOP__epRISC_coreEmu__machine.__PVT__core__DOT__rRegM = 0U;
    }
    // ALWAYS at ../../../firmware/core/core_v5r0.v:411
    if (vlTOPp->iBoardReset) {
	if ((3U == (IData)(vlSymsp->TOP__epRISC_coreEmu__machine.__PVT__core__DOT__rPipeState))) {
	    vlSymsp->TOP__epRISC_coreEmu__machine.__PVT__core__DOT__rRegR 
		= vlSymsp->TOP__epRISC_coreEmu__machine.__PVT__core__DOT__rALUOut;
	}
    } else {
	vlSymsp->TOP__epRISC_coreEmu__machine.__PVT__core__DOT__rRegR = VL_ULL(0);
    }
    // ALWAYS at ../../../firmware/core/core_v5r0.v:366
    if (vlTOPp->iBoardReset) {
	if ((2U == (IData)(vlSymsp->TOP__epRISC_coreEmu__machine.__PVT__core__DOT__rPipeState))) {
	    vlSymsp->TOP__epRISC_coreEmu__machine.__PVT__core__DOT__rRegB 
		= ((0x80000000U & vlSymsp->TOP__epRISC_coreEmu__machine.__PVT__core__DOT__rInst)
		    ? ((0x80000U & vlSymsp->TOP__epRISC_coreEmu__machine.__PVT__core__DOT__rInst)
		        ? ((IData)(0xfff00000U) + (0xfffffU 
						   & vlSymsp->TOP__epRISC_coreEmu__machine.__PVT__core__DOT__rInst))
		        : (0xfffffU & vlSymsp->TOP__epRISC_coreEmu__machine.__PVT__core__DOT__rInst))
		    : ((1U == (3U & (vlSymsp->TOP__epRISC_coreEmu__machine.__PVT__core__DOT__rInst 
				     >> 0x1eU))) ? 
		       ((0x20U & vlSymsp->TOP__epRISC_coreEmu__machine.__PVT__core__DOT__rRegCS)
			 ? ((IData)(0xfff00000U) + 
			    (0xfffffU & vlSymsp->TOP__epRISC_coreEmu__machine.__PVT__core__DOT__rInst))
			 : (0xfffffU & vlSymsp->TOP__epRISC_coreEmu__machine.__PVT__core__DOT__rInst))
		        : ((1U == (7U & (vlSymsp->TOP__epRISC_coreEmu__machine.__PVT__core__DOT__rInst 
					 >> 0x1dU)))
			    ? ((0xfffffU & vlSymsp->TOP__epRISC_coreEmu__machine.__PVT__core__DOT__rInst) 
			       << (0x1eU & (vlSymsp->TOP__epRISC_coreEmu__machine.__PVT__core__DOT__rInst 
					    >> 0x13U)))
			    : ((((1U == (0xfU & (vlSymsp->TOP__epRISC_coreEmu__machine.__PVT__core__DOT__rInst 
						 >> 0x1cU))) 
				 & (~ (IData)(vlSymsp->TOP__epRISC_coreEmu__machine.__PVT__core__DOT__mALURegisters))) 
				& ((0xcU == (0x1fU 
					     & (vlSymsp->TOP__epRISC_coreEmu__machine.__PVT__core__DOT__rInst 
						>> 0x14U))) 
				   | (0xdU == (0x1fU 
					       & (vlSymsp->TOP__epRISC_coreEmu__machine.__PVT__core__DOT__rInst 
						  >> 0x14U)))))
			        ? (0x1eU & (vlSymsp->TOP__epRISC_coreEmu__machine.__PVT__core__DOT__rInst 
					    >> 7U))
			        : (((1U == (0xfU & 
					    (vlSymsp->TOP__epRISC_coreEmu__machine.__PVT__core__DOT__rInst 
					     >> 0x1cU))) 
				    & (~ (IData)(vlSymsp->TOP__epRISC_coreEmu__machine.__PVT__core__DOT__mALURegisters)))
				    ? ((0xffU & vlSymsp->TOP__epRISC_coreEmu__machine.__PVT__core__DOT__rInst) 
				       << (0x1eU & 
					   (vlSymsp->TOP__epRISC_coreEmu__machine.__PVT__core__DOT__rInst 
					    >> 7U)))
				    : vlSymsp->TOP__epRISC_coreEmu__machine.__PVT__core__DOT__wBusInB)))));
	}
    } else {
	vlSymsp->TOP__epRISC_coreEmu__machine.__PVT__core__DOT__rRegB = 0U;
    }
    // ALWAYS at ../../../firmware/core/core_v5r0.v:356
    if (vlTOPp->iBoardReset) {
	if ((2U == (IData)(vlSymsp->TOP__epRISC_coreEmu__machine.__PVT__core__DOT__rPipeState))) {
	    vlSymsp->TOP__epRISC_coreEmu__machine.__PVT__core__DOT__rRegA 
		= (((0U == (IData)(vlSymsp->TOP__epRISC_coreEmu__machine.__PVT__core__DOT__wBusInAddrA)) 
		    & (~ (vlSymsp->TOP__epRISC_coreEmu__machine.__PVT__core__DOT__rRegCS 
			  >> 7U))) ? vlSymsp->TOP__epRISC_coreEmu__machine.__PVT__core__DOT__rRegIP
		    : (((1U == (IData)(vlSymsp->TOP__epRISC_coreEmu__machine.__PVT__core__DOT__wBusInAddrA)) 
			& (~ (vlSymsp->TOP__epRISC_coreEmu__machine.__PVT__core__DOT__rRegCS 
			      >> 7U))) ? (((IData)(vlSymsp->TOP__epRISC_coreEmu__machine.__PVT__core__DOT__mLoadLoad) 
					   & (2U == 
					      (0xfU 
					       & (vlSymsp->TOP__epRISC_coreEmu__machine.__PVT__core__DOT__rInst 
						  >> 0x18U))))
					   ? (vlSymsp->TOP__epRISC_coreEmu__machine.__PVT__core__DOT__rRegSP 
					      - (IData)(1U))
					   : vlSymsp->TOP__epRISC_coreEmu__machine.__PVT__core__DOT__rRegSP)
		        : (((2U == (IData)(vlSymsp->TOP__epRISC_coreEmu__machine.__PVT__core__DOT__wBusInAddrA)) 
			    & (~ (vlSymsp->TOP__epRISC_coreEmu__machine.__PVT__core__DOT__rRegCS 
				  >> 7U))) ? vlSymsp->TOP__epRISC_coreEmu__machine.__PVT__core__DOT__rRegCS
			    : (((3U == (IData)(vlSymsp->TOP__epRISC_coreEmu__machine.__PVT__core__DOT__wBusInAddrA)) 
				& (~ (vlSymsp->TOP__epRISC_coreEmu__machine.__PVT__core__DOT__rRegCS 
				      >> 7U))) ? vlSymsp->TOP__epRISC_coreEmu__machine.__PVT__core__DOT__rRegGL
			        : (((0xfU == (0xfU 
					      & (vlSymsp->TOP__epRISC_coreEmu__machine.__PVT__core__DOT__rRegCS 
						 >> 0xcU))) 
				    & (4U == (IData)(vlSymsp->TOP__epRISC_coreEmu__machine.__PVT__core__DOT__wBusInAddrA)))
				    ? vlSymsp->TOP__epRISC_coreEmu__machine.__PVT__core__DOT__rRegInterruptBase
				    : vlSymsp->TOP__epRISC_coreEmu__machine.__PVT__core__DOT__wBusRegA)))));
	}
    } else {
	vlSymsp->TOP__epRISC_coreEmu__machine.__PVT__core__DOT__rRegA = 0U;
    }
    vlSymsp->TOP__epRISC_coreEmu__machine.__PVT__core__DOT__rRegSP 
	= vlSymsp->TOP__epRISC_coreEmu__machine.__Vdly__core__DOT__rRegSP;
    vlSymsp->TOP__epRISC_coreEmu__machine.__PVT__core__DOT__rRegIP 
	= vlSymsp->TOP__epRISC_coreEmu__machine.__Vdly__core__DOT__rRegIP;
    // ALWAYS at ../../../firmware/core/core_v5r0.v:341
    if (vlTOPp->iBoardReset) {
	if ((5U == (IData)(vlSymsp->TOP__epRISC_coreEmu__machine.__PVT__core__DOT__rPipeState))) {
	    if ((((~ (vlSymsp->TOP__epRISC_coreEmu__machine.__PVT__core__DOT__rRegCS 
		      >> 7U)) & (3U == (IData)(vlSymsp->TOP__epRISC_coreEmu__machine.__PVT__core__DOT__wBusOutAddrA))) 
		 & (IData)(vlSymsp->TOP__epRISC_coreEmu__machine.__PVT__core__DOT__wBusOutWriteA))) {
		vlSymsp->TOP__epRISC_coreEmu__machine.__PVT__core__DOT__rRegGL 
		    = vlSymsp->TOP__epRISC_coreEmu__machine.__PVT__core__DOT__wBusOutA;
	    } else {
		if ((((~ (vlSymsp->TOP__epRISC_coreEmu__machine.__PVT__core__DOT__rRegCS 
			  >> 7U)) & (3U == (IData)(vlSymsp->TOP__epRISC_coreEmu__machine.__PVT__core__DOT__wBusOutAddrB))) 
		     & (IData)(vlSymsp->TOP__epRISC_coreEmu__machine.__PVT__core__DOT__wBusOutWriteB))) {
		    vlSymsp->TOP__epRISC_coreEmu__machine.__PVT__core__DOT__rRegGL 
			= vlSymsp->TOP__epRISC_coreEmu__machine.__PVT__core__DOT__wBusOutB;
		}
	    }
	}
    } else {
	vlSymsp->TOP__epRISC_coreEmu__machine.__PVT__core__DOT__rRegGL = 0U;
    }
    // ALWAYS at ../../../firmware/core/core_v5r0.v:472
    if (vlTOPp->iBoardReset) {
	if ((5U == (IData)(vlSymsp->TOP__epRISC_coreEmu__machine.__PVT__core__DOT__rPipeState))) {
	    if ((((0xfU == (0xfU & (vlSymsp->TOP__epRISC_coreEmu__machine.__PVT__core__DOT__rRegCS 
				    >> 0xcU))) & (4U 
						  == (IData)(vlSymsp->TOP__epRISC_coreEmu__machine.__PVT__core__DOT__wBusOutAddrA))) 
		 & (IData)(vlSymsp->TOP__epRISC_coreEmu__machine.__PVT__core__DOT__wBusOutWriteA))) {
		vlSymsp->TOP__epRISC_coreEmu__machine.__PVT__core__DOT__rRegInterruptBase 
		    = vlSymsp->TOP__epRISC_coreEmu__machine.__PVT__core__DOT__wBusOutA;
	    }
	    if ((((0xfU == (0xfU & (vlSymsp->TOP__epRISC_coreEmu__machine.__PVT__core__DOT__rRegCS 
				    >> 0xcU))) & (4U 
						  == (IData)(vlSymsp->TOP__epRISC_coreEmu__machine.__PVT__core__DOT__wBusOutAddrB))) 
		 & (IData)(vlSymsp->TOP__epRISC_coreEmu__machine.__PVT__core__DOT__wBusOutWriteB))) {
		vlSymsp->TOP__epRISC_coreEmu__machine.__PVT__core__DOT__rRegInterruptBase 
		    = vlSymsp->TOP__epRISC_coreEmu__machine.__PVT__core__DOT__wBusOutB;
	    }
	}
    } else {
	vlSymsp->TOP__epRISC_coreEmu__machine.__PVT__core__DOT__rRegInterruptBase = 0U;
    }
    // ALWAYS at ../../../firmware/core/core_v5r0.v:402
    if (vlTOPp->iBoardReset) {
	if ((1U == (IData)(vlSymsp->TOP__epRISC_coreEmu__machine.__PVT__core__DOT__rPipeState))) {
	    vlSymsp->TOP__epRISC_coreEmu__machine.__PVT__core__DOT__rInst 
		= vlSymsp->TOP__epRISC_coreEmu__machine.__PVT__wCoreBusData;
	}
    } else {
	vlSymsp->TOP__epRISC_coreEmu__machine.__PVT__core__DOT__rInst = 0U;
    }
    vlSymsp->TOP__epRISC_coreEmu__machine.__PVT__core__DOT__rRegCS 
	= vlSymsp->TOP__epRISC_coreEmu__machine.__Vdly__core__DOT__rRegCS;
    vlSymsp->TOP__epRISC_coreEmu__machine.__PVT__core__DOT__fCSHideRegs 
	= (1U & (vlSymsp->TOP__epRISC_coreEmu__machine.__PVT__core__DOT__rRegCS 
		 >> 7U));
    vlSymsp->TOP__epRISC_coreEmu__machine.__PVT__core__DOT__fCSFlagSet 
	= (1U & (~ (vlSymsp->TOP__epRISC_coreEmu__machine.__PVT__core__DOT__rRegCS 
		    >> 4U)));
    vlSymsp->TOP__epRISC_coreEmu__machine.__PVT__core__DOT__mBranchInterrupt 
	= ((vlSymsp->TOP__epRISC_coreEmu__machine.__PVT__core__DOT__rInst 
	    >> 0x1fU) & (3U == (7U & (vlSymsp->TOP__epRISC_coreEmu__machine.__PVT__core__DOT__rInst 
				      >> 0x1cU))));
    vlSymsp->TOP__epRISC_coreEmu__machine.__PVT__core__DOT__mALURegisters 
	= ((1U == (0xfU & (vlSymsp->TOP__epRISC_coreEmu__machine.__PVT__core__DOT__rInst 
			   >> 0x1cU))) & (~ (vlSymsp->TOP__epRISC_coreEmu__machine.__PVT__core__DOT__rInst 
					     >> 0x1bU)));
    vlSymsp->TOP__epRISC_coreEmu__machine.__PVT__core__DOT__wBusInAddrA 
	= ((0x80000000U & vlSymsp->TOP__epRISC_coreEmu__machine.__PVT__core__DOT__rInst)
	    ? (0xfU & (vlSymsp->TOP__epRISC_coreEmu__machine.__PVT__core__DOT__rInst 
		       >> 0x14U)) : ((1U == (3U & (vlSymsp->TOP__epRISC_coreEmu__machine.__PVT__core__DOT__rInst 
						   >> 0x1eU)))
				      ? (0xfU & (vlSymsp->TOP__epRISC_coreEmu__machine.__PVT__core__DOT__rInst 
						 >> 0x18U))
				      : ((1U == (7U 
						 & (vlSymsp->TOP__epRISC_coreEmu__machine.__PVT__core__DOT__rInst 
						    >> 0x1dU)))
					  ? (0xfU & 
					     (vlSymsp->TOP__epRISC_coreEmu__machine.__PVT__core__DOT__rInst 
					      >> 0x18U))
					  : ((1U == 
					      (0xfU 
					       & (vlSymsp->TOP__epRISC_coreEmu__machine.__PVT__core__DOT__rInst 
						  >> 0x1cU)))
					      ? (0xfU 
						 & (vlSymsp->TOP__epRISC_coreEmu__machine.__PVT__core__DOT__rInst 
						    >> 0xcU))
					      : ((1U 
						  == 
						  (0x1fU 
						   & (vlSymsp->TOP__epRISC_coreEmu__machine.__PVT__core__DOT__rInst 
						      >> 0x1bU)))
						  ? 
						 (0xfU 
						  & (vlSymsp->TOP__epRISC_coreEmu__machine.__PVT__core__DOT__rInst 
						     >> 0x14U))
						  : 0xffU)))));
    vlSymsp->TOP__epRISC_coreEmu__machine.__PVT__core__DOT__wBusOutAddrA 
	= ((1U == (0x1fU & (vlSymsp->TOP__epRISC_coreEmu__machine.__PVT__core__DOT__rInst 
			    >> 0x1bU))) ? (0xfU & (vlSymsp->TOP__epRISC_coreEmu__machine.__PVT__core__DOT__rInst 
						   >> 0x10U))
	    : ((1U == (0xfU & (vlSymsp->TOP__epRISC_coreEmu__machine.__PVT__core__DOT__rInst 
			       >> 0x1cU))) ? (0xfU 
					      & (vlSymsp->TOP__epRISC_coreEmu__machine.__PVT__core__DOT__rInst 
						 >> 0x10U))
	        : ((1U == (3U & (vlSymsp->TOP__epRISC_coreEmu__machine.__PVT__core__DOT__rInst 
				 >> 0x1eU))) ? (0xfU 
						& (vlSymsp->TOP__epRISC_coreEmu__machine.__PVT__core__DOT__rInst 
						   >> 0x14U))
		    : 0xffU)));
    vlSymsp->TOP__epRISC_coreEmu__machine.__PVT__core__DOT__wBusOutAddrB 
	= ((1U == (0x1fU & (vlSymsp->TOP__epRISC_coreEmu__machine.__PVT__core__DOT__rInst 
			    >> 0x1bU))) ? (0xfU & (vlSymsp->TOP__epRISC_coreEmu__machine.__PVT__core__DOT__rInst 
						   >> 0x14U))
	    : ((1U == (7U & (vlSymsp->TOP__epRISC_coreEmu__machine.__PVT__core__DOT__rInst 
			     >> 0x1dU))) ? (0xfU & 
					    (vlSymsp->TOP__epRISC_coreEmu__machine.__PVT__core__DOT__rInst 
					     >> 0x18U))
	        : 0xffU));
    // ALWAYS at ../../../firmware/core/core_v5r0.v:446
    vlSymsp->TOP__epRISC_coreEmu__machine.__Vtableidx1 
	= ((0x100U & (vlSymsp->TOP__epRISC_coreEmu__machine.__PVT__core__DOT__rRegCS 
		      << 8U)) | ((0x80U & (vlSymsp->TOP__epRISC_coreEmu__machine.__PVT__core__DOT__rRegCS 
					   << 6U)) 
				 | ((0x40U & (vlSymsp->TOP__epRISC_coreEmu__machine.__PVT__core__DOT__rRegCS 
					      << 3U)) 
				    | ((0x20U & (vlSymsp->TOP__epRISC_coreEmu__machine.__PVT__core__DOT__rRegCS 
						 << 3U)) 
				       | ((0x1eU & 
					   (vlSymsp->TOP__epRISC_coreEmu__machine.__PVT__core__DOT__rInst 
					    >> 0x17U)) 
					  | (1U & (vlSymsp->TOP__epRISC_coreEmu__machine.__PVT__core__DOT__rInst 
						   >> 0x1fU)))))));
    vlSymsp->TOP__epRISC_coreEmu__machine.__PVT__core__DOT__rExec 
	= vlSymsp->TOP__epRISC_coreEmu__machine.__Vtable1___PVT__core__DOT__rExec
	[vlSymsp->TOP__epRISC_coreEmu__machine.__Vtableidx1];
    vlSymsp->TOP__epRISC_coreEmu__machine.__PVT__core__DOT__wBusInAddrB 
	= ((1U == (3U & (vlSymsp->TOP__epRISC_coreEmu__machine.__PVT__core__DOT__rInst 
			 >> 0x1eU))) ? (0xfU & (vlSymsp->TOP__epRISC_coreEmu__machine.__PVT__core__DOT__rInst 
						>> 0x14U))
	    : ((1U == (0xfU & (vlSymsp->TOP__epRISC_coreEmu__machine.__PVT__core__DOT__rInst 
			       >> 0x1cU))) ? (0xfU 
					      & (vlSymsp->TOP__epRISC_coreEmu__machine.__PVT__core__DOT__rInst 
						 >> 8U))
	        : ((1U == (0x1fU & (vlSymsp->TOP__epRISC_coreEmu__machine.__PVT__core__DOT__rInst 
				    >> 0x1bU))) ? (0xfU 
						   & (vlSymsp->TOP__epRISC_coreEmu__machine.__PVT__core__DOT__rInst 
						      >> 0x10U))
		    : 0xffU)));
    vlSymsp->TOP__epRISC_coreEmu__machine.__PVT__core__DOT__mDirectOR 
	= ((1U == (7U & (vlSymsp->TOP__epRISC_coreEmu__machine.__PVT__core__DOT__rInst 
			 >> 0x1dU))) & (vlSymsp->TOP__epRISC_coreEmu__machine.__PVT__core__DOT__rInst 
					>> 0x1cU));
    vlSymsp->TOP__epRISC_coreEmu__machine.__PVT__core__DOT__mBranchLoadStack 
	= ((vlSymsp->TOP__epRISC_coreEmu__machine.__PVT__core__DOT__rInst 
	    >> 0x1fU) & (7U == (7U & (vlSymsp->TOP__epRISC_coreEmu__machine.__PVT__core__DOT__rInst 
				      >> 0x1cU))));
    vlSymsp->TOP__epRISC_coreEmu__machine.__PVT__core__DOT__mLoadLoad 
	= ((1U == (3U & (vlSymsp->TOP__epRISC_coreEmu__machine.__PVT__core__DOT__rInst 
			 >> 0x1eU))) & (~ (vlSymsp->TOP__epRISC_coreEmu__machine.__PVT__core__DOT__rInst 
					   >> 0x1dU)));
    vlSymsp->TOP__epRISC_coreEmu__machine.__PVT__core__DOT__mBranchSaveStack 
	= ((vlSymsp->TOP__epRISC_coreEmu__machine.__PVT__core__DOT__rInst 
	    >> 0x1fU) & (5U == (7U & (vlSymsp->TOP__epRISC_coreEmu__machine.__PVT__core__DOT__rInst 
				      >> 0x1cU))));
    vlSymsp->TOP__epRISC_coreEmu__machine.__PVT__core__DOT__mLoadStore 
	= ((1U == (3U & (vlSymsp->TOP__epRISC_coreEmu__machine.__PVT__core__DOT__rInst 
			 >> 0x1eU))) & (vlSymsp->TOP__epRISC_coreEmu__machine.__PVT__core__DOT__rInst 
					>> 0x1dU));
}

void VepRISC_coreEmu_epRISC_machine::_initial__TOP__epRISC_coreEmu__machine__7(VepRISC_coreEmu__Syms* __restrict vlSymsp) {
    VL_DEBUG_IF(VL_PRINTF("        VepRISC_coreEmu_epRISC_machine::_initial__TOP__epRISC_coreEmu__machine__7\n"); );
    VepRISC_coreEmu* __restrict vlTOPp VL_ATTR_UNUSED = vlSymsp->TOPp;
    // Body
    // INITIAL at ../../../firmware/core/rom_v1r0.v:15
    vlSymsp->TOP__epRISC_coreEmu__machine.__PVT__tbrom__DOT__rContents[0U] = 0x8000001fU;
    vlSymsp->TOP__epRISC_coreEmu__machine.__PVT__tbrom__DOT__rContents[1U] = 0x43f01ff0U;
    vlSymsp->TOP__epRISC_coreEmu__machine.__PVT__tbrom__DOT__rContents[2U] = 0x61f00000U;
    vlSymsp->TOP__epRISC_coreEmu__machine.__PVT__tbrom__DOT__rContents[3U] = 0xd0000296U;
    vlSymsp->TOP__epRISC_coreEmu__machine.__PVT__tbrom__DOT__rContents[4U] = 0x63f01ff1U;
    vlSymsp->TOP__epRISC_coreEmu__machine.__PVT__tbrom__DOT__rContents[5U] = 0x41f00000U;
    vlSymsp->TOP__epRISC_coreEmu__machine.__PVT__tbrom__DOT__rContents[6U] = 0xf0000000U;
    vlSymsp->TOP__epRISC_coreEmu__machine.__PVT__tbrom__DOT__rContents[7U] = 0xd00002b4U;
    vlSymsp->TOP__epRISC_coreEmu__machine.__PVT__tbrom__DOT__rContents[8U] = 0x63f01ff1U;
    vlSymsp->TOP__epRISC_coreEmu__machine.__PVT__tbrom__DOT__rContents[9U] = 0xf0000000U;
    vlSymsp->TOP__epRISC_coreEmu__machine.__PVT__tbrom__DOT__rContents[0xaU] = 0x43f01ff2U;
    vlSymsp->TOP__epRISC_coreEmu__machine.__PVT__tbrom__DOT__rContents[0xbU] = 0x61f00000U;
    vlSymsp->TOP__epRISC_coreEmu__machine.__PVT__tbrom__DOT__rContents[0xcU] = 0x43f01ff3U;
    vlSymsp->TOP__epRISC_coreEmu__machine.__PVT__tbrom__DOT__rContents[0xdU] = 0x61f00000U;
    vlSymsp->TOP__epRISC_coreEmu__machine.__PVT__tbrom__DOT__rContents[0xeU] = 0xd00003e1U;
    vlSymsp->TOP__epRISC_coreEmu__machine.__PVT__tbrom__DOT__rContents[0xfU] = 0x63f01ff4U;
    vlSymsp->TOP__epRISC_coreEmu__machine.__PVT__tbrom__DOT__rContents[0x10U] = 0x41f00000U;
    vlSymsp->TOP__epRISC_coreEmu__machine.__PVT__tbrom__DOT__rContents[0x11U] = 0x41f00000U;
    vlSymsp->TOP__epRISC_coreEmu__machine.__PVT__tbrom__DOT__rContents[0x12U] = 0xf0000000U;
    vlSymsp->TOP__epRISC_coreEmu__machine.__PVT__tbrom__DOT__rContents[0x13U] = 0x43f01ff2U;
    vlSymsp->TOP__epRISC_coreEmu__machine.__PVT__tbrom__DOT__rContents[0x14U] = 0x61f00000U;
    vlSymsp->TOP__epRISC_coreEmu__machine.__PVT__tbrom__DOT__rContents[0x15U] = 0x43f01ff3U;
    vlSymsp->TOP__epRISC_coreEmu__machine.__PVT__tbrom__DOT__rContents[0x16U] = 0x61f00000U;
    vlSymsp->TOP__epRISC_coreEmu__machine.__PVT__tbrom__DOT__rContents[0x17U] = 0xd000040dU;
    vlSymsp->TOP__epRISC_coreEmu__machine.__PVT__tbrom__DOT__rContents[0x18U] = 0x63f01ff4U;
    vlSymsp->TOP__epRISC_coreEmu__machine.__PVT__tbrom__DOT__rContents[0x19U] = 0x41f00000U;
    vlSymsp->TOP__epRISC_coreEmu__machine.__PVT__tbrom__DOT__rContents[0x1aU] = 0x41f00000U;
    vlSymsp->TOP__epRISC_coreEmu__machine.__PVT__tbrom__DOT__rContents[0x1bU] = 0xf0000000U;
    vlSymsp->TOP__epRISC_coreEmu__machine.__PVT__tbrom__DOT__rContents[0x1cU] = 0xd0000338U;
    vlSymsp->TOP__epRISC_coreEmu__machine.__PVT__tbrom__DOT__rContents[0x1dU] = 0x63f01ff5U;
    vlSymsp->TOP__epRISC_coreEmu__machine.__PVT__tbrom__DOT__rContents[0x1eU] = 0xf0000000U;
    vlSymsp->TOP__epRISC_coreEmu__machine.__PVT__tbrom__DOT__rContents[0x1fU] = 0x21001100U;
    vlSymsp->TOP__epRISC_coreEmu__machine.__PVT__tbrom__DOT__rContents[0x20U] = 0x23000000U;
    vlSymsp->TOP__epRISC_coreEmu__machine.__PVT__tbrom__DOT__rContents[0x21U] = 0xd00001cdU;
    vlSymsp->TOP__epRISC_coreEmu__machine.__PVT__tbrom__DOT__rContents[0x22U] = 0x24007fffU;
    vlSymsp->TOP__epRISC_coreEmu__machine.__PVT__tbrom__DOT__rContents[0x23U] = 0x61400000U;
    vlSymsp->TOP__epRISC_coreEmu__machine.__PVT__tbrom__DOT__rContents[0x24U] = 0x24000000U;
    vlSymsp->TOP__epRISC_coreEmu__machine.__PVT__tbrom__DOT__rContents[0x25U] = 0x61400000U;
    vlSymsp->TOP__epRISC_coreEmu__machine.__PVT__tbrom__DOT__rContents[0x26U] = 0xd00001d8U;
    vlSymsp->TOP__epRISC_coreEmu__machine.__PVT__tbrom__DOT__rContents[0x27U] = 0x41400000U;
    vlSymsp->TOP__epRISC_coreEmu__machine.__PVT__tbrom__DOT__rContents[0x28U] = 0x41400000U;
    vlSymsp->TOP__epRISC_coreEmu__machine.__PVT__tbrom__DOT__rContents[0x29U] = 0x2400012aU;
    vlSymsp->TOP__epRISC_coreEmu__machine.__PVT__tbrom__DOT__rContents[0x2aU] = 0x61400000U;
    vlSymsp->TOP__epRISC_coreEmu__machine.__PVT__tbrom__DOT__rContents[0x2bU] = 0xd00002faU;
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
    vlSymsp->TOP__epRISC_coreEmu__machine.__PVT__tbrom__DOT__rContents[0x118U] = 0xd000030cU;
    vlSymsp->TOP__epRISC_coreEmu__machine.__PVT__tbrom__DOT__rContents[0x119U] = 0x41500000U;
    vlSymsp->TOP__epRISC_coreEmu__machine.__PVT__tbrom__DOT__rContents[0x11aU] = 0x41700000U;
    vlSymsp->TOP__epRISC_coreEmu__machine.__PVT__tbrom__DOT__rContents[0x11bU] = 0x18e0f000U;
    vlSymsp->TOP__epRISC_coreEmu__machine.__PVT__tbrom__DOT__rContents[0x11cU] = 0x82000009U;
    vlSymsp->TOP__epRISC_coreEmu__machine.__PVT__tbrom__DOT__rContents[0x11dU] = 0x18055001U;
    vlSymsp->TOP__epRISC_coreEmu__machine.__PVT__tbrom__DOT__rContents[0x11eU] = 0x18077080U;
    vlSymsp->TOP__epRISC_coreEmu__machine.__PVT__tbrom__DOT__rContents[0x11fU] = 0x18166001U;
    vlSymsp->TOP__epRISC_coreEmu__machine.__PVT__tbrom__DOT__rContents[0x120U] = 0x18e06000U;
    vlSymsp->TOP__epRISC_coreEmu__machine.__PVT__tbrom__DOT__rContents[0x121U] = 0x820ffff5U;
    vlSymsp->TOP__epRISC_coreEmu__machine.__PVT__tbrom__DOT__rContents[0x122U] = 0xd00003a4U;
    vlSymsp->TOP__epRISC_coreEmu__machine.__PVT__tbrom__DOT__rContents[0x123U] = 0x48700005U;
    vlSymsp->TOP__epRISC_coreEmu__machine.__PVT__tbrom__DOT__rContents[0x124U] = 0x80700000U;
    vlSymsp->TOP__epRISC_coreEmu__machine.__PVT__tbrom__DOT__rContents[0x125U] = 0x240001e6U;
    vlSymsp->TOP__epRISC_coreEmu__machine.__PVT__tbrom__DOT__rContents[0x126U] = 0x61400000U;
    vlSymsp->TOP__epRISC_coreEmu__machine.__PVT__tbrom__DOT__rContents[0x127U] = 0xd00001feU;
    vlSymsp->TOP__epRISC_coreEmu__machine.__PVT__tbrom__DOT__rContents[0x128U] = 0x41400000U;
    vlSymsp->TOP__epRISC_coreEmu__machine.__PVT__tbrom__DOT__rContents[0x129U] = 0x80000496U;
    vlSymsp->TOP__epRISC_coreEmu__machine.__PVT__tbrom__DOT__rContents[0x12aU] = 0x65705249U;
    vlSymsp->TOP__epRISC_coreEmu__machine.__PVT__tbrom__DOT__rContents[0x12bU] = 0x53432042U;
    vlSymsp->TOP__epRISC_coreEmu__machine.__PVT__tbrom__DOT__rContents[0x12cU] = 0x6f6f746cU;
    vlSymsp->TOP__epRISC_coreEmu__machine.__PVT__tbrom__DOT__rContents[0x12dU] = 0x6f616465U;
    vlSymsp->TOP__epRISC_coreEmu__machine.__PVT__tbrom__DOT__rContents[0x12eU] = 0x72207633U;
    vlSymsp->TOP__epRISC_coreEmu__machine.__PVT__tbrom__DOT__rContents[0x12fU] = 0x2e340a0dU;
    vlSymsp->TOP__epRISC_coreEmu__machine.__PVT__tbrom__DOT__rContents[0x130U] = 0x636f7079U;
    vlSymsp->TOP__epRISC_coreEmu__machine.__PVT__tbrom__DOT__rContents[0x131U] = 0x72696768U;
    vlSymsp->TOP__epRISC_coreEmu__machine.__PVT__tbrom__DOT__rContents[0x132U] = 0x74203230U;
    vlSymsp->TOP__epRISC_coreEmu__machine.__PVT__tbrom__DOT__rContents[0x133U] = 0x31352d32U;
    vlSymsp->TOP__epRISC_coreEmu__machine.__PVT__tbrom__DOT__rContents[0x134U] = 0x30313720U;
    vlSymsp->TOP__epRISC_coreEmu__machine.__PVT__tbrom__DOT__rContents[0x135U] = 0x50726f70U;
    vlSymsp->TOP__epRISC_coreEmu__machine.__PVT__tbrom__DOT__rContents[0x136U] = 0x6f727469U;
    vlSymsp->TOP__epRISC_coreEmu__machine.__PVT__tbrom__DOT__rContents[0x137U] = 0x6f6e616cU;
    vlSymsp->TOP__epRISC_coreEmu__machine.__PVT__tbrom__DOT__rContents[0x138U] = 0x204c6162U;
    vlSymsp->TOP__epRISC_coreEmu__machine.__PVT__tbrom__DOT__rContents[0x139U] = 0x730a0d0aU;
    vlSymsp->TOP__epRISC_coreEmu__machine.__PVT__tbrom__DOT__rContents[0x13aU] = 0xd000000U;
    vlSymsp->TOP__epRISC_coreEmu__machine.__PVT__tbrom__DOT__rContents[0x13bU] = 0x41747465U;
    vlSymsp->TOP__epRISC_coreEmu__machine.__PVT__tbrom__DOT__rContents[0x13cU] = 0x6d707469U;
    vlSymsp->TOP__epRISC_coreEmu__machine.__PVT__tbrom__DOT__rContents[0x13dU] = 0x6e672074U;
    vlSymsp->TOP__epRISC_coreEmu__machine.__PVT__tbrom__DOT__rContents[0x13eU] = 0x6f206d6fU;
    vlSymsp->TOP__epRISC_coreEmu__machine.__PVT__tbrom__DOT__rContents[0x13fU] = 0x756e7420U;
    vlSymsp->TOP__epRISC_coreEmu__machine.__PVT__tbrom__DOT__rContents[0x140U] = 0x53442063U;
    vlSymsp->TOP__epRISC_coreEmu__machine.__PVT__tbrom__DOT__rContents[0x141U] = 0x61726420U;
    vlSymsp->TOP__epRISC_coreEmu__machine.__PVT__tbrom__DOT__rContents[0x142U] = 0x696e2073U;
    vlSymsp->TOP__epRISC_coreEmu__machine.__PVT__tbrom__DOT__rContents[0x143U] = 0x6c6f7420U;
    vlSymsp->TOP__epRISC_coreEmu__machine.__PVT__tbrom__DOT__rContents[0x144U] = 0x412e2e2eU;
    vlSymsp->TOP__epRISC_coreEmu__machine.__PVT__tbrom__DOT__rContents[0x145U] = 0xa0d0000U;
    vlSymsp->TOP__epRISC_coreEmu__machine.__PVT__tbrom__DOT__rContents[0x146U] = 0x41747465U;
    vlSymsp->TOP__epRISC_coreEmu__machine.__PVT__tbrom__DOT__rContents[0x147U] = 0x6d707469U;
    vlSymsp->TOP__epRISC_coreEmu__machine.__PVT__tbrom__DOT__rContents[0x148U] = 0x6e672074U;
    vlSymsp->TOP__epRISC_coreEmu__machine.__PVT__tbrom__DOT__rContents[0x149U] = 0x6f206d6fU;
    vlSymsp->TOP__epRISC_coreEmu__machine.__PVT__tbrom__DOT__rContents[0x14aU] = 0x756e7420U;
    vlSymsp->TOP__epRISC_coreEmu__machine.__PVT__tbrom__DOT__rContents[0x14bU] = 0x53442063U;
    vlSymsp->TOP__epRISC_coreEmu__machine.__PVT__tbrom__DOT__rContents[0x14cU] = 0x61726420U;
    vlSymsp->TOP__epRISC_coreEmu__machine.__PVT__tbrom__DOT__rContents[0x14dU] = 0x696e2073U;
    vlSymsp->TOP__epRISC_coreEmu__machine.__PVT__tbrom__DOT__rContents[0x14eU] = 0x6c6f7420U;
    vlSymsp->TOP__epRISC_coreEmu__machine.__PVT__tbrom__DOT__rContents[0x14fU] = 0x422e2e2eU;
    vlSymsp->TOP__epRISC_coreEmu__machine.__PVT__tbrom__DOT__rContents[0x150U] = 0xa0d0000U;
    vlSymsp->TOP__epRISC_coreEmu__machine.__PVT__tbrom__DOT__rContents[0x151U] = 0x20205344U;
    vlSymsp->TOP__epRISC_coreEmu__machine.__PVT__tbrom__DOT__rContents[0x152U] = 0x20636172U;
    vlSymsp->TOP__epRISC_coreEmu__machine.__PVT__tbrom__DOT__rContents[0x153U] = 0x64206d6fU;
    vlSymsp->TOP__epRISC_coreEmu__machine.__PVT__tbrom__DOT__rContents[0x154U] = 0x756e7465U;
    vlSymsp->TOP__epRISC_coreEmu__machine.__PVT__tbrom__DOT__rContents[0x155U] = 0x64207375U;
    vlSymsp->TOP__epRISC_coreEmu__machine.__PVT__tbrom__DOT__rContents[0x156U] = 0x63636573U;
    vlSymsp->TOP__epRISC_coreEmu__machine.__PVT__tbrom__DOT__rContents[0x157U] = 0x7366756cU;
    vlSymsp->TOP__epRISC_coreEmu__machine.__PVT__tbrom__DOT__rContents[0x158U] = 0x6c792e0aU;
    vlSymsp->TOP__epRISC_coreEmu__machine.__PVT__tbrom__DOT__rContents[0x159U] = 0xd0a0d00U;
    vlSymsp->TOP__epRISC_coreEmu__machine.__PVT__tbrom__DOT__rContents[0x15aU] = 0x20204572U;
    vlSymsp->TOP__epRISC_coreEmu__machine.__PVT__tbrom__DOT__rContents[0x15bU] = 0x726f7220U;
    vlSymsp->TOP__epRISC_coreEmu__machine.__PVT__tbrom__DOT__rContents[0x15cU] = 0x6d6f756eU;
    vlSymsp->TOP__epRISC_coreEmu__machine.__PVT__tbrom__DOT__rContents[0x15dU] = 0x74696e67U;
    vlSymsp->TOP__epRISC_coreEmu__machine.__PVT__tbrom__DOT__rContents[0x15eU] = 0x20534420U;
    vlSymsp->TOP__epRISC_coreEmu__machine.__PVT__tbrom__DOT__rContents[0x15fU] = 0x63617264U;
    vlSymsp->TOP__epRISC_coreEmu__machine.__PVT__tbrom__DOT__rContents[0x160U] = 0x2e0a0d0aU;
    vlSymsp->TOP__epRISC_coreEmu__machine.__PVT__tbrom__DOT__rContents[0x161U] = 0xd000000U;
    vlSymsp->TOP__epRISC_coreEmu__machine.__PVT__tbrom__DOT__rContents[0x162U] = 0x46657463U;
    vlSymsp->TOP__epRISC_coreEmu__machine.__PVT__tbrom__DOT__rContents[0x163U] = 0x68696e67U;
    vlSymsp->TOP__epRISC_coreEmu__machine.__PVT__tbrom__DOT__rContents[0x164U] = 0x20646973U;
    vlSymsp->TOP__epRISC_coreEmu__machine.__PVT__tbrom__DOT__rContents[0x165U] = 0x6b20696eU;
    vlSymsp->TOP__epRISC_coreEmu__machine.__PVT__tbrom__DOT__rContents[0x166U] = 0x666f2e2eU;
    vlSymsp->TOP__epRISC_coreEmu__machine.__PVT__tbrom__DOT__rContents[0x167U] = 0x2e0a0d00U;
    vlSymsp->TOP__epRISC_coreEmu__machine.__PVT__tbrom__DOT__rContents[0x168U] = 0x20204469U;
    vlSymsp->TOP__epRISC_coreEmu__machine.__PVT__tbrom__DOT__rContents[0x169U] = 0x736b2061U;
    vlSymsp->TOP__epRISC_coreEmu__machine.__PVT__tbrom__DOT__rContents[0x16aU] = 0x70706561U;
    vlSymsp->TOP__epRISC_coreEmu__machine.__PVT__tbrom__DOT__rContents[0x16bU] = 0x72732074U;
    vlSymsp->TOP__epRISC_coreEmu__machine.__PVT__tbrom__DOT__rContents[0x16cU] = 0x6f206265U;
    vlSymsp->TOP__epRISC_coreEmu__machine.__PVT__tbrom__DOT__rContents[0x16dU] = 0x20636f72U;
    vlSymsp->TOP__epRISC_coreEmu__machine.__PVT__tbrom__DOT__rContents[0x16eU] = 0x72757074U;
    vlSymsp->TOP__epRISC_coreEmu__machine.__PVT__tbrom__DOT__rContents[0x16fU] = 0x2e0a0d0aU;
    vlSymsp->TOP__epRISC_coreEmu__machine.__PVT__tbrom__DOT__rContents[0x170U] = 0xd000000U;
    vlSymsp->TOP__epRISC_coreEmu__machine.__PVT__tbrom__DOT__rContents[0x171U] = 0x2020466fU;
    vlSymsp->TOP__epRISC_coreEmu__machine.__PVT__tbrom__DOT__rContents[0x172U] = 0x756e6420U;
    vlSymsp->TOP__epRISC_coreEmu__machine.__PVT__tbrom__DOT__rContents[0x173U] = 0x6469736bU;
    vlSymsp->TOP__epRISC_coreEmu__machine.__PVT__tbrom__DOT__rContents[0x174U] = 0x20270000U;
    vlSymsp->TOP__epRISC_coreEmu__machine.__PVT__tbrom__DOT__rContents[0x175U] = 0x27206174U;
    vlSymsp->TOP__epRISC_coreEmu__machine.__PVT__tbrom__DOT__rContents[0x176U] = 0x20626c6fU;
    vlSymsp->TOP__epRISC_coreEmu__machine.__PVT__tbrom__DOT__rContents[0x177U] = 0x636b2030U;
    vlSymsp->TOP__epRISC_coreEmu__machine.__PVT__tbrom__DOT__rContents[0x178U] = 0x2e0a0d00U;
    vlSymsp->TOP__epRISC_coreEmu__machine.__PVT__tbrom__DOT__rContents[0x179U] = 0x20204469U;
    vlSymsp->TOP__epRISC_coreEmu__machine.__PVT__tbrom__DOT__rContents[0x17aU] = 0x736b2061U;
    vlSymsp->TOP__epRISC_coreEmu__machine.__PVT__tbrom__DOT__rContents[0x17bU] = 0x70706561U;
    vlSymsp->TOP__epRISC_coreEmu__machine.__PVT__tbrom__DOT__rContents[0x17cU] = 0x72732074U;
    vlSymsp->TOP__epRISC_coreEmu__machine.__PVT__tbrom__DOT__rContents[0x17dU] = 0x6f206265U;
    vlSymsp->TOP__epRISC_coreEmu__machine.__PVT__tbrom__DOT__rContents[0x17eU] = 0x20656d70U;
    vlSymsp->TOP__epRISC_coreEmu__machine.__PVT__tbrom__DOT__rContents[0x17fU] = 0x74792e0aU;
    vlSymsp->TOP__epRISC_coreEmu__machine.__PVT__tbrom__DOT__rContents[0x180U] = 0xd0a0d00U;
    vlSymsp->TOP__epRISC_coreEmu__machine.__PVT__tbrom__DOT__rContents[0x181U] = 0x2020466fU;
    vlSymsp->TOP__epRISC_coreEmu__machine.__PVT__tbrom__DOT__rContents[0x182U] = 0x756e6420U;
    vlSymsp->TOP__epRISC_coreEmu__machine.__PVT__tbrom__DOT__rContents[0x183U] = 0U;
    vlSymsp->TOP__epRISC_coreEmu__machine.__PVT__tbrom__DOT__rContents[0x184U] = 0x20656e74U;
    vlSymsp->TOP__epRISC_coreEmu__machine.__PVT__tbrom__DOT__rContents[0x185U] = 0x72696573U;
    vlSymsp->TOP__epRISC_coreEmu__machine.__PVT__tbrom__DOT__rContents[0x186U] = 0x206f6e20U;
    vlSymsp->TOP__epRISC_coreEmu__machine.__PVT__tbrom__DOT__rContents[0x187U] = 0x6469736bU;
    vlSymsp->TOP__epRISC_coreEmu__machine.__PVT__tbrom__DOT__rContents[0x188U] = 0x2e0a0d0aU;
    vlSymsp->TOP__epRISC_coreEmu__machine.__PVT__tbrom__DOT__rContents[0x189U] = 0xd000000U;
    vlSymsp->TOP__epRISC_coreEmu__machine.__PVT__tbrom__DOT__rContents[0x18aU] = 0x41766169U;
    vlSymsp->TOP__epRISC_coreEmu__machine.__PVT__tbrom__DOT__rContents[0x18bU] = 0x6c61626cU;
    vlSymsp->TOP__epRISC_coreEmu__machine.__PVT__tbrom__DOT__rContents[0x18cU] = 0x6520656eU;
    vlSymsp->TOP__epRISC_coreEmu__machine.__PVT__tbrom__DOT__rContents[0x18dU] = 0x74726965U;
    vlSymsp->TOP__epRISC_coreEmu__machine.__PVT__tbrom__DOT__rContents[0x18eU] = 0x733a0a0dU;
    vlSymsp->TOP__epRISC_coreEmu__machine.__PVT__tbrom__DOT__rContents[0x18fU] = 0U;
    vlSymsp->TOP__epRISC_coreEmu__machine.__PVT__tbrom__DOT__rContents[0x190U] = 0x3a20456eU;
    vlSymsp->TOP__epRISC_coreEmu__machine.__PVT__tbrom__DOT__rContents[0x191U] = 0x74727920U;
    vlSymsp->TOP__epRISC_coreEmu__machine.__PVT__tbrom__DOT__rContents[0x192U] = 0x27000000U;
    vlSymsp->TOP__epRISC_coreEmu__machine.__PVT__tbrom__DOT__rContents[0x193U] = 0x273a2073U;
    vlSymsp->TOP__epRISC_coreEmu__machine.__PVT__tbrom__DOT__rContents[0x194U] = 0x74617274U;
    vlSymsp->TOP__epRISC_coreEmu__machine.__PVT__tbrom__DOT__rContents[0x195U] = 0x20000000U;
    vlSymsp->TOP__epRISC_coreEmu__machine.__PVT__tbrom__DOT__rContents[0x196U] = 0x2c206c65U;
    vlSymsp->TOP__epRISC_coreEmu__machine.__PVT__tbrom__DOT__rContents[0x197U] = 0x6e677468U;
    vlSymsp->TOP__epRISC_coreEmu__machine.__PVT__tbrom__DOT__rContents[0x198U] = 0x20000000U;
    vlSymsp->TOP__epRISC_coreEmu__machine.__PVT__tbrom__DOT__rContents[0x199U] = 0x2c206c6fU;
    vlSymsp->TOP__epRISC_coreEmu__machine.__PVT__tbrom__DOT__rContents[0x19aU] = 0x61642000U;
    vlSymsp->TOP__epRISC_coreEmu__machine.__PVT__tbrom__DOT__rContents[0x19bU] = 0x53656c65U;
    vlSymsp->TOP__epRISC_coreEmu__machine.__PVT__tbrom__DOT__rContents[0x19cU] = 0x63742061U;
    vlSymsp->TOP__epRISC_coreEmu__machine.__PVT__tbrom__DOT__rContents[0x19dU] = 0x6e20656eU;
    vlSymsp->TOP__epRISC_coreEmu__machine.__PVT__tbrom__DOT__rContents[0x19eU] = 0x74727920U;
    vlSymsp->TOP__epRISC_coreEmu__machine.__PVT__tbrom__DOT__rContents[0x19fU] = 0x746f2065U;
    vlSymsp->TOP__epRISC_coreEmu__machine.__PVT__tbrom__DOT__rContents[0x1a0U] = 0x78656375U;
    vlSymsp->TOP__epRISC_coreEmu__machine.__PVT__tbrom__DOT__rContents[0x1a1U] = 0x74652c20U;
    vlSymsp->TOP__epRISC_coreEmu__machine.__PVT__tbrom__DOT__rContents[0x1a2U] = 0x6f722074U;
    vlSymsp->TOP__epRISC_coreEmu__machine.__PVT__tbrom__DOT__rContents[0x1a3U] = 0x79706520U;
    vlSymsp->TOP__epRISC_coreEmu__machine.__PVT__tbrom__DOT__rContents[0x1a4U] = 0x274d2720U;
    vlSymsp->TOP__epRISC_coreEmu__machine.__PVT__tbrom__DOT__rContents[0x1a5U] = 0x746f2065U;
    vlSymsp->TOP__epRISC_coreEmu__machine.__PVT__tbrom__DOT__rContents[0x1a6U] = 0x6e746572U;
    vlSymsp->TOP__epRISC_coreEmu__machine.__PVT__tbrom__DOT__rContents[0x1a7U] = 0x20746865U;
    vlSymsp->TOP__epRISC_coreEmu__machine.__PVT__tbrom__DOT__rContents[0x1a8U] = 0x206d6f6eU;
    vlSymsp->TOP__epRISC_coreEmu__machine.__PVT__tbrom__DOT__rContents[0x1a9U] = 0x69746f72U;
    vlSymsp->TOP__epRISC_coreEmu__machine.__PVT__tbrom__DOT__rContents[0x1aaU] = 0x3a200000U;
    vlSymsp->TOP__epRISC_coreEmu__machine.__PVT__tbrom__DOT__rContents[0x1abU] = 0x20204c6fU;
    vlSymsp->TOP__epRISC_coreEmu__machine.__PVT__tbrom__DOT__rContents[0x1acU] = 0x6164696eU;
    vlSymsp->TOP__epRISC_coreEmu__machine.__PVT__tbrom__DOT__rContents[0x1adU] = 0x6720656eU;
    vlSymsp->TOP__epRISC_coreEmu__machine.__PVT__tbrom__DOT__rContents[0x1aeU] = 0x7472792eU;
    vlSymsp->TOP__epRISC_coreEmu__machine.__PVT__tbrom__DOT__rContents[0x1afU] = 0x2e2e0a0dU;
    vlSymsp->TOP__epRISC_coreEmu__machine.__PVT__tbrom__DOT__rContents[0x1b0U] = 0xa0d0000U;
    vlSymsp->TOP__epRISC_coreEmu__machine.__PVT__tbrom__DOT__rContents[0x1b1U] = 0x53746172U;
    vlSymsp->TOP__epRISC_coreEmu__machine.__PVT__tbrom__DOT__rContents[0x1b2U] = 0x74696e67U;
    vlSymsp->TOP__epRISC_coreEmu__machine.__PVT__tbrom__DOT__rContents[0x1b3U] = 0x20504f53U;
    vlSymsp->TOP__epRISC_coreEmu__machine.__PVT__tbrom__DOT__rContents[0x1b4U] = 0x54732e2eU;
    vlSymsp->TOP__epRISC_coreEmu__machine.__PVT__tbrom__DOT__rContents[0x1b5U] = 0x2e0a0d00U;
    vlSymsp->TOP__epRISC_coreEmu__machine.__PVT__tbrom__DOT__rContents[0x1b6U] = 0x20204d65U;
    vlSymsp->TOP__epRISC_coreEmu__machine.__PVT__tbrom__DOT__rContents[0x1b7U] = 0x6d6f7279U;
    vlSymsp->TOP__epRISC_coreEmu__machine.__PVT__tbrom__DOT__rContents[0x1b8U] = 0x20202020U;
    vlSymsp->TOP__epRISC_coreEmu__machine.__PVT__tbrom__DOT__rContents[0x1b9U] = 0x20202020U;
    vlSymsp->TOP__epRISC_coreEmu__machine.__PVT__tbrom__DOT__rContents[0x1baU] = 0x20200000U;
    vlSymsp->TOP__epRISC_coreEmu__machine.__PVT__tbrom__DOT__rContents[0x1bbU] = 0x20205541U;
    vlSymsp->TOP__epRISC_coreEmu__machine.__PVT__tbrom__DOT__rContents[0x1bcU] = 0x52542020U;
    vlSymsp->TOP__epRISC_coreEmu__machine.__PVT__tbrom__DOT__rContents[0x1bdU] = 0x20202020U;
    vlSymsp->TOP__epRISC_coreEmu__machine.__PVT__tbrom__DOT__rContents[0x1beU] = 0x20202020U;
    vlSymsp->TOP__epRISC_coreEmu__machine.__PVT__tbrom__DOT__rContents[0x1bfU] = 0x20200000U;
    vlSymsp->TOP__epRISC_coreEmu__machine.__PVT__tbrom__DOT__rContents[0x1c0U] = 0x20205350U;
    vlSymsp->TOP__epRISC_coreEmu__machine.__PVT__tbrom__DOT__rContents[0x1c1U] = 0x49202020U;
    vlSymsp->TOP__epRISC_coreEmu__machine.__PVT__tbrom__DOT__rContents[0x1c2U] = 0x20202020U;
    vlSymsp->TOP__epRISC_coreEmu__machine.__PVT__tbrom__DOT__rContents[0x1c3U] = 0x20202020U;
    vlSymsp->TOP__epRISC_coreEmu__machine.__PVT__tbrom__DOT__rContents[0x1c4U] = 0x20200000U;
    vlSymsp->TOP__epRISC_coreEmu__machine.__PVT__tbrom__DOT__rContents[0x1c5U] = 0x20207379U;
    vlSymsp->TOP__epRISC_coreEmu__machine.__PVT__tbrom__DOT__rContents[0x1c6U] = 0x73582042U;
    vlSymsp->TOP__epRISC_coreEmu__machine.__PVT__tbrom__DOT__rContents[0x1c7U] = 0x75732020U;
    vlSymsp->TOP__epRISC_coreEmu__machine.__PVT__tbrom__DOT__rContents[0x1c8U] = 0x20202020U;
    vlSymsp->TOP__epRISC_coreEmu__machine.__PVT__tbrom__DOT__rContents[0x1c9U] = 0x20200000U;
    vlSymsp->TOP__epRISC_coreEmu__machine.__PVT__tbrom__DOT__rContents[0x1caU] = 0x2020492fU;
    vlSymsp->TOP__epRISC_coreEmu__machine.__PVT__tbrom__DOT__rContents[0x1cbU] = 0x4f20436fU;
    vlSymsp->TOP__epRISC_coreEmu__machine.__PVT__tbrom__DOT__rContents[0x1ccU] = 0x6e74726fU;
    vlSymsp->TOP__epRISC_coreEmu__machine.__PVT__tbrom__DOT__rContents[0x1cdU] = 0x6c6c6572U;
    vlSymsp->TOP__epRISC_coreEmu__machine.__PVT__tbrom__DOT__rContents[0x1ceU] = 0x20200000U;
    vlSymsp->TOP__epRISC_coreEmu__machine.__PVT__tbrom__DOT__rContents[0x1cfU] = 0x4f4b0a0dU;
    vlSymsp->TOP__epRISC_coreEmu__machine.__PVT__tbrom__DOT__rContents[0x1d0U] = 0U;
    vlSymsp->TOP__epRISC_coreEmu__machine.__PVT__tbrom__DOT__rContents[0x1d1U] = 0x4641494cU;
    vlSymsp->TOP__epRISC_coreEmu__machine.__PVT__tbrom__DOT__rContents[0x1d2U] = 0xa0d0000U;
    vlSymsp->TOP__epRISC_coreEmu__machine.__PVT__tbrom__DOT__rContents[0x1d3U] = 0x2020504fU;
    vlSymsp->TOP__epRISC_coreEmu__machine.__PVT__tbrom__DOT__rContents[0x1d4U] = 0x53542073U;
    vlSymsp->TOP__epRISC_coreEmu__machine.__PVT__tbrom__DOT__rContents[0x1d5U] = 0x75636365U;
    vlSymsp->TOP__epRISC_coreEmu__machine.__PVT__tbrom__DOT__rContents[0x1d6U] = 0x73736675U;
    vlSymsp->TOP__epRISC_coreEmu__machine.__PVT__tbrom__DOT__rContents[0x1d7U] = 0x6c2e0a0dU;
    vlSymsp->TOP__epRISC_coreEmu__machine.__PVT__tbrom__DOT__rContents[0x1d8U] = 0xa0d0000U;
    vlSymsp->TOP__epRISC_coreEmu__machine.__PVT__tbrom__DOT__rContents[0x1d9U] = 0x2020504fU;
    vlSymsp->TOP__epRISC_coreEmu__machine.__PVT__tbrom__DOT__rContents[0x1daU] = 0x53542075U;
    vlSymsp->TOP__epRISC_coreEmu__machine.__PVT__tbrom__DOT__rContents[0x1dbU] = 0x6e737563U;
    vlSymsp->TOP__epRISC_coreEmu__machine.__PVT__tbrom__DOT__rContents[0x1dcU] = 0x63657373U;
    vlSymsp->TOP__epRISC_coreEmu__machine.__PVT__tbrom__DOT__rContents[0x1ddU] = 0x66756c2eU;
    vlSymsp->TOP__epRISC_coreEmu__machine.__PVT__tbrom__DOT__rContents[0x1deU] = 0xa0d0a0dU;
    vlSymsp->TOP__epRISC_coreEmu__machine.__PVT__tbrom__DOT__rContents[0x1dfU] = 0U;
    vlSymsp->TOP__epRISC_coreEmu__machine.__PVT__tbrom__DOT__rContents[0x1e0U] = 0x2020504fU;
    vlSymsp->TOP__epRISC_coreEmu__machine.__PVT__tbrom__DOT__rContents[0x1e1U] = 0x53547320U;
    vlSymsp->TOP__epRISC_coreEmu__machine.__PVT__tbrom__DOT__rContents[0x1e2U] = 0x636f6d70U;
    vlSymsp->TOP__epRISC_coreEmu__machine.__PVT__tbrom__DOT__rContents[0x1e3U] = 0x6c657465U;
    vlSymsp->TOP__epRISC_coreEmu__machine.__PVT__tbrom__DOT__rContents[0x1e4U] = 0x2e0a0d0aU;
    vlSymsp->TOP__epRISC_coreEmu__machine.__PVT__tbrom__DOT__rContents[0x1e5U] = 0xd000000U;
    vlSymsp->TOP__epRISC_coreEmu__machine.__PVT__tbrom__DOT__rContents[0x1e6U] = 0x456e7465U;
    vlSymsp->TOP__epRISC_coreEmu__machine.__PVT__tbrom__DOT__rContents[0x1e7U] = 0x72696e67U;
    vlSymsp->TOP__epRISC_coreEmu__machine.__PVT__tbrom__DOT__rContents[0x1e8U] = 0x206d6f6eU;
    vlSymsp->TOP__epRISC_coreEmu__machine.__PVT__tbrom__DOT__rContents[0x1e9U] = 0x69746f72U;
    vlSymsp->TOP__epRISC_coreEmu__machine.__PVT__tbrom__DOT__rContents[0x1eaU] = 0x2e2e2e0aU;
    vlSymsp->TOP__epRISC_coreEmu__machine.__PVT__tbrom__DOT__rContents[0x1ebU] = 0xd0a0d00U;
    vlSymsp->TOP__epRISC_coreEmu__machine.__PVT__tbrom__DOT__rContents[0x1ecU] = 0xa0d0000U;
    vlSymsp->TOP__epRISC_coreEmu__machine.__PVT__tbrom__DOT__rContents[0x1edU] = 0x20200000U;
    vlSymsp->TOP__epRISC_coreEmu__machine.__PVT__tbrom__DOT__rContents[0x1eeU] = 0x61c00000U;
    vlSymsp->TOP__epRISC_coreEmu__machine.__PVT__tbrom__DOT__rContents[0x1efU] = 0x2c002000U;
    vlSymsp->TOP__epRISC_coreEmu__machine.__PVT__tbrom__DOT__rContents[0x1f0U] = 0x2f010001U;
    vlSymsp->TOP__epRISC_coreEmu__machine.__PVT__tbrom__DOT__rContents[0x1f1U] = 0x6cf00000U;
    vlSymsp->TOP__epRISC_coreEmu__machine.__PVT__tbrom__DOT__rContents[0x1f2U] = 0x4000000U;
    vlSymsp->TOP__epRISC_coreEmu__machine.__PVT__tbrom__DOT__rContents[0x1f3U] = 0x4000000U;
    vlSymsp->TOP__epRISC_coreEmu__machine.__PVT__tbrom__DOT__rContents[0x1f4U] = 0x4000000U;
    vlSymsp->TOP__epRISC_coreEmu__machine.__PVT__tbrom__DOT__rContents[0x1f5U] = 0x4000000U;
    vlSymsp->TOP__epRISC_coreEmu__machine.__PVT__tbrom__DOT__rContents[0x1f6U] = 0x4cf00000U;
    vlSymsp->TOP__epRISC_coreEmu__machine.__PVT__tbrom__DOT__rContents[0x1f7U] = 0x18f0f001U;
    vlSymsp->TOP__epRISC_coreEmu__machine.__PVT__tbrom__DOT__rContents[0x1f8U] = 0x820ffffeU;
    vlSymsp->TOP__epRISC_coreEmu__machine.__PVT__tbrom__DOT__rContents[0x1f9U] = 0x4cf00000U;
    vlSymsp->TOP__epRISC_coreEmu__machine.__PVT__tbrom__DOT__rContents[0x1faU] = 0x18f0f002U;
    vlSymsp->TOP__epRISC_coreEmu__machine.__PVT__tbrom__DOT__rContents[0x1fbU] = 0x820ffffeU;
    vlSymsp->TOP__epRISC_coreEmu__machine.__PVT__tbrom__DOT__rContents[0x1fcU] = 0x41c00000U;
    vlSymsp->TOP__epRISC_coreEmu__machine.__PVT__tbrom__DOT__rContents[0x1fdU] = 0xf0000000U;
    vlSymsp->TOP__epRISC_coreEmu__machine.__PVT__tbrom__DOT__rContents[0x1feU] = 0x61e00000U;
    vlSymsp->TOP__epRISC_coreEmu__machine.__PVT__tbrom__DOT__rContents[0x1ffU] = 0x61d00000U;
    vlSymsp->TOP__epRISC_coreEmu__machine.__PVT__tbrom__DOT__rContents[0x200U] = 0x61c00000U;
    vlSymsp->TOP__epRISC_coreEmu__machine.__PVT__tbrom__DOT__rContents[0x201U] = 0x18111004U;
    vlSymsp->TOP__epRISC_coreEmu__machine.__PVT__tbrom__DOT__rContents[0x202U] = 0x2c002000U;
    vlSymsp->TOP__epRISC_coreEmu__machine.__PVT__tbrom__DOT__rContents[0x203U] = 0x41d00000U;
    vlSymsp->TOP__epRISC_coreEmu__machine.__PVT__tbrom__DOT__rContents[0x204U] = 0x41e00000U;
    vlSymsp->TOP__epRISC_coreEmu__machine.__PVT__tbrom__DOT__rContents[0x205U] = 0x18011006U;
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
    vlSymsp->TOP__epRISC_coreEmu__machine.__PVT__tbrom__DOT__rContents[0x368U] = 0x2d000001U;
    vlSymsp->TOP__epRISC_coreEmu__machine.__PVT__tbrom__DOT__rContents[0x369U] = 0x186dd000U;
    vlSymsp->TOP__epRISC_coreEmu__machine.__PVT__tbrom__DOT__rContents[0x36aU] = 0x2e000000U;
    vlSymsp->TOP__epRISC_coreEmu__machine.__PVT__tbrom__DOT__rContents[0x36bU] = 0xd0000084U;
    vlSymsp->TOP__epRISC_coreEmu__machine.__PVT__tbrom__DOT__rContents[0x36cU] = 0x10e0fd00U;
    vlSymsp->TOP__epRISC_coreEmu__machine.__PVT__tbrom__DOT__rContents[0x36dU] = 0x81000005U;
    vlSymsp->TOP__epRISC_coreEmu__machine.__PVT__tbrom__DOT__rContents[0x36eU] = 0x180ee001U;
    vlSymsp->TOP__epRISC_coreEmu__machine.__PVT__tbrom__DOT__rContents[0x36fU] = 0x18e0e402U;
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
