JCLemme/eprisc-open-computer/firmware/io/video_v1r0.v

/* verilator lint_off WIDTH */

module epRISC_VideoTerm(iClk, iRst, iAddr, iData, oData, iWrite, iEnable, iMemClk, iVideoClk, oColor, oHS, oVS);

    input iClk, iRst, iWrite, iEnable, iMemClk, iVideoClk;
    input [1:0] iAddr;
    input [15:0] iData;
    output wire [7:0] oColor;
    output reg oHS, oVS;
    output wire [15:0] oData;
    
    reg [3:0] rRowSel;
    reg [7:0] rDataOutput, rColorOutput;
    reg [9:0] rPulseX, rPulseY;
    reg [11:0] rTempX, rTempY, rFramePtr;
    reg [15:0] rConfig, rRow, rColumn;
    
    wire mDrawingValidLine, mDrawingValidFrame, mDrawingValidData;
    wire [7:0] wCurrColor, wCurrChar, wFontRow;
    wire [9:0] wPixelX, wPixelY;
    wire [15:0] wCharRAMData, wCharRAMFrame;
        
    assign oData = (!iEnable) ? 16'bz : ((iAddr==0)?rConfig:((iAddr==1)?rColumn:((iAddr==2)?rRow:((iAddr==3)?wCharRAMData:16'b1))));
    
    assign oColor = (rDataOutput[7-wPixelX[2:0]] && mDrawingValidData) ? rColorOutput : 8'h0; //either color or black
    //(mDrawingValidData && ((wPixelX[0] && wPixelY[0]) || (!wPixelX[0] && !wPixelY[0]))) ? 8'hFF : 8'h0; //this is a fine-checkerboard test pattern

    assign mDrawingValidLine = (rPulseY >= 35 && rPulseY < 515) ? 1 : 0;
    assign mDrawingValidFrame = (rPulseX >= 160 && rPulseX < 800) ? 1 : 0;
    assign mDrawingValidData = (mDrawingValidLine && mDrawingValidFrame) ? 1 : 0;
    
    assign wPixelX = rPulseX - 10'd160;
    assign wPixelY = rPulseY - 10'd35;
       
    assign wCurrColor = wCharRAMFrame[15:8];
    assign wCurrChar = wCharRAMFrame[7:0];
    
    wire [16:0] debug;
    assign debug = (rRow<<4)+(rRow<<6)+rColumn;
    
    `ifdef EMULATED
    SoftVideoRAM vram((rRow<<4)+(rRow<<6)+rColumn, rFramePtr[11:0], iClk, iMemClk, iData, 16'h0, (iWrite&&iEnable&&iAddr==3)?1:0, 0, wCharRAMData, wCharRAMFrame);
    `else
    ChipVideoRAM vram((rRow<<4)+(rRow<<6)+rColumn, rFramePtr[11:0], iClk, iMemClk, iData, 16'h0, (iWrite&&iEnable&&iAddr==3)?1:0, 0, wCharRAMData, wCharRAMFrame);
    `endif
    
    VideoROM vrom({rRowSel, wCurrChar}, iMemClk, wFontRow);
    
    always @(posedge iClk) begin
        if(iRst) begin
            rConfig <= 16'h0;
        end else begin
            if(iWrite && iEnable && (iAddr == 0))
                rConfig <= iData;
        end
    end

    always @(posedge iClk) begin
        if(iRst) begin
            rRow <= 16'h0;
        end else begin
            if(iWrite && iEnable && (iAddr == 2))
                rRow <= iData;
        end
    end
    
    always @(posedge iClk) begin
        if(iRst) begin
            rColumn <= 16'h0;
        end else begin
            if(iWrite && iEnable && (iAddr == 1))
                rColumn <= iData;
        end
    end
        
    always @(posedge iVideoClk) begin
        if(iRst) begin
            rPulseX <= 0;
            rPulseY <= 0;
            rRowSel <= 0;
        end else begin
            rPulseX <= rPulseX + 1;
            
            case(rPulseX)
                0: oHS <= 1;
                16: oHS <= 0;
                112: oHS <= 1;
                800: begin rPulseY <= rPulseY + 1; rRowSel <= rRowSel + 1; rPulseX <= 0; end
            endcase
            
            case(rPulseY)
                0: oVS <= 1;
                10: oVS <= 0;
                12: oVS <= 1;
                525: begin rPulseY <= 0; rRowSel <= 0; end
            endcase
            
            if(rRowSel == 12)
                rRowSel <= 0;
        end
    end

    always @(posedge iVideoClk) begin
        if(iRst) begin
            rDataOutput <= 0;
            rFramePtr <= 0;
        end else begin
            //rFramePtr <= 0;
            
            case(wPixelX[2:0])
                3'h6: begin
                    if(rPulseX < 154) begin
                        rTempX <= 0;
                    end else if(rPulseX >= 154 && rPulseX < 160) begin
                        rTempX <= 1;
                    end else begin
                        rTempX <= 2 + (wPixelX / 8);
                    end
                    
                    rTempY <= wPixelY / 12;
                    rFramePtr <= (rTempY * 80) + rTempX;
                end
                
                3'h7: begin
                    rDataOutput <= wFontRow;
                    rColorOutput <= wCurrColor;
                end
            endcase
        end
    end
    
endmodule

module SoftVideoRAM(iAddrA, iAddrB, iClkA, iClkB, iDInA, iDInB, iWriteA, iWriteB, oDOutA, oDOutB);
    input iClkA, iClkB, iWriteA, iWriteB;
    input [11:0] iAddrA, iAddrB;
    input [15:0] iDInA, iDInB;
    output reg [15:0] oDOutA, oDOutB;
    
    reg [12:0] rClr;
    reg [15:0] rContents[0:4095];

    wire debug;
    assign debug = (iAddrB > 80) ? 1 : 0;
    
    initial begin
        for(rClr=0;rClr<4096;rClr=rClr+1)
            rContents[rClr] = 0;
    end
    
    always @(posedge iClkA) begin
        if(iWriteA) begin
            rContents[iAddrA] <= iDInA;
        end
    end
    
    always @(posedge iClkB) begin
        if(iWriteB) begin
            rContents[iAddrB] <= iDInB;
        end
    end
    
    always @(posedge iClkA) begin
        if(!iWriteA) begin
            oDOutA <= rContents[iAddrA];
        end
    end
    
    always @(posedge iClkB) begin
        if(!iWriteB) begin
            oDOutB <= rContents[iAddrB];
        end
    end
endmodule

module VideoROM(iAddr, iClk, oData);

    input iClk;
    input [11:0] iAddr;
    output wire [15:0] oData;
    
    reg [15:0] rDataOut, rContents[0:3071];
    
    assign oData = rDataOut;
    
    always @(posedge iClk) begin
        rDataOut = rContents[iAddr];
    end
    
    initial begin
        rContents[0] = 8'b01010101;
        rContents[1] = 8'b10101010;
        rContents[2] = 8'b01010101;
        rContents[3] = 8'b11111111;
        rContents[4] = 8'b11111111;
        rContents[5] = 8'b00000000;
        rContents[6] = 8'b11111110;
        rContents[7] = 8'b11111110;
        rContents[8] = 8'b00111000;
        rContents[9] = 8'b01111100;
        rContents[10] = 8'b01111100;
        rContents[11] = 8'b01101100;
        rContents[12] = 8'b00010000;
        rContents[13] = 8'b00111000;
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
        rContents[2953] = 8'b11110000;
        rContents[2954] = 8'b00001111;
        rContents[2955] = 8'b00000000;
        rContents[2956] = 8'b11111111;
        rContents[2957] = 8'b00011000;
        rContents[2958] = 8'b00000000;
        rContents[2959] = 8'b00011000;
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
