JCLemme/eprisc-open-computer/software/application/microchess.asm

; epRISC development platform - MicroChess
;
; modified by John C. Lemme, jclemme (at) proportionallabs (dot) com
; this file is *not* part of the epRISC project, but rather an open-source project that is included here as part of the baseline system - see "license.txt" for details.
;
; John Lemme's port of Daryl Rictor's port of Peter Jenning's MicroChess. 


;***********************************************************************
;
;  MicroChess (c) 1996-2002 Peter Jennings, peterj@benlo.com 
;
;***********************************************************************
; I have been given permission to distribute this program by the
; author and copyright holder, Peter Jennings.  Please get his 
; permission if you wish to re-distribute a modified copy of 
; this file to others.  He specifically requested that his 
; copyright notice be included in the source and binary images.
; Thanks! 
;
; When life gives you lemons, squeeze them back into life's eyes - Elmer
; modified by Daryl Rictor to work over a serial terminal connection, August 2002.


; 6551 I/O Port Addresses
;
ACIADat	= 	$7F70
ACIASta	=	$7F71
ACIACmd	=	$7F72
ACIACtl	=	$7F73
;
; page zero variables
;
BOARD   =	$50 
BK      =	$60 
PIECE   =	$B0 
SQUARE  =	$B1 
SP2     =	$B2 
SP1     =	$B3 
INCHEK  =	$B4 
STATE   =	$B5 
MOVEN   =	$B6 
REV	=       $B7
OMOVE   =	$DC 
WCAP0   =	$DD 
COUNT   =	$DE 
BCAP2   =	$DE 
WCAP2   =	$DF 
BCAP1   =	$E0 
WCAP1   =	$E1 
BCAP0   =	$E2 
MOB     =	$E3 
MAXC    =	$E4 
CC      =	$E5 
PCAP    =	$E6 
BMOB    =	$E3 
BMAXC   =	$E4 
BMCC    =	$E5 		; was BCC (TASS doesn't like it as a label)
BMAXP   =	$E6 
XMAXC   =	$E8 
WMOB    =	$EB 
WMAXC   =	$EC 
WCC     =	$ED 
WMAXP   =	$EE 
PMOB    =	$EF 
PMAXC   =	$F0 
PCC     =	$F1 
PCP     =	$F2 
OLDKY   =	$F3 
BESTP   =	$FB 
BESTV   =	$FA 
BESTM   =	$F9 
DIS1    =	$FB 
DIS2    =	$FA 
DIS3    =	$F9 
temp    =   $FC

!ip h00004000                                       ; load into RAM @ $1000-$15FF (really @ h4000)

:entry      move.v  d:%GL v:#h5000                  ; (This is to emulate zero page behavior)
            move.v  d:%Xw v:#h00                    ; LDA   #$00		        ; REVERSE TOGGLE
		    stor.o  r:%GL s:%Xw o:REV               ; STA   REV
            call.s  a:chess_ioinit                  ; JSR   Init_6551
:chess		                                        ; CLD			            ; INITIALIZE (not applicable for epRISC)
		    move.v  d:%SP v:#h1800                  ; LDX   #$FF		        ; TWO STACKS (just make sure stack is OK in case bootloader effed up)
		                                            ; TXS	
		    move.v  d:%Xx v:#hC8                    ; LDX	#$C8
		    stor.o  r:%GL s:%Xx o:SP2               ; STX	SP2
		
                                                                                ; ROUTINES TO LIGHT LED
                                                                                ; DISPLAY AND GET KEY
                                                                                ; FROM KEYBOARD
		
:out		call.s  a:pout                          ; JSR	pout		        ; DISPLAY AND
		    call.s  a:kin                           ; JSR	KIN		            ; GET INPUT   *** my routine waits for a keypress
                                                    ; CMP	OLDKY		        ; KEY IN ACC  *** no need to debounce
                                                    ; BEQ	OUT		            ; (DEBOUNCE)
                                                    ; STA	OLDKY
                                                    		
		    cmpr.v  a:%Xw v:#h43                    ; CMP	#$43		        ; [C]
		    brch.a  c:%NEQ a:noset                  ; BNE	NOSET		        ; SET UP
		    move.v  d:%Xx v:#h1F                    ; LDX	#$1F		        ; BOARD
:whset		move.v  d:%Xz v:SETW                    
            addr.r  d:%Xz a:%Xz b:%Xx
            load.o  r:%Xz d:%Xw                     ; LDA	SETW,X		        ; FROM
		    move.v  d:%Xz v:BOARD                   
		    addr.r  d:%Xz a:%Xz b:%Xx 
		    stor.o  r:%Xz s:%Xw                     ; STA	BOARD,X		        ; SETW
		    subr.v  d:%Xx a:%Xx v:#h01              ; DEX	
		    cmpr.v  a:%Xw v:#h00
		    brch.a  c:%POS a:whset                  ; BPL	WHSET
		    move.v  d:%Xx v:#h1B                    ; LDX	#$1B		        ; *ADDED
		    stor.o  r:%GL s:%Xx o:OMOVE             ; STX	OMOVE		        ; INITS TO $FF
		    move.v  d:%Xw v:#hCC                    ; LDA	#$CC		        ; Display CCC
		    cmpr.v  a:%Xw v:#h00    
		    brch.a  c:%NEQ a:cldsp                  ; BNE	CLDSP
		
:noset		cmpr.v  a:%Xw v:#h45                    ; CMP	#$45		        ; [E]
		    brch.a  c:%NEQ a:norev                  ; BNE	NOREV		        ; REVERSE
		    call.s  a:reverse                       ; JSR	REVERSE        	    ; BOARD IS
		                                            ; SEC                       ; (pretty pretty sure I don't need this)
		    move.v  d:%Xw v:#h01                    ; LDA	#$01
		    load.o  r:%GL d:%Xz o:REV
		    subr.r  d:%Xw a:%Xw b:%Xz               ; SBC	REV
		    stor.o  r:%GL s:%Xw o:REV               ; STA	REV		            ; TOGGLE REV FLAG
		    move.v  d:%Xw v:#hEE                    ; LDA	#$EE                ; IS
		    cmpr.v  a:%Xw v:#h00                    
		    brch.a  c:%NEQ a:cldsp                  ; BNE	CLDSP
	
:norev		cmpr.v  a:%Xw v:#h40			        ; [P]
		    brch.a  c:%NEQ a:nogo                   ; BNE	NOGO           	    ; PLAY CHESS
		    call.s  a:go                            ; JSR	GO
:cldsp		stor.o  r:%GL s:%Xw o:DIS1              ; STA	DIS1          	    ; DISPLAY
		    stor.o  r:%GL s:%Xw o:DIS2              ; STA	DIS2         	    ; ACROSS
		    stor.o  r:%GL s:%Xw o:DIS3              ; STA	DIS3          	    ; DISPLAY
		    cmpr.v  a:%Xw v:#h00
		    brch.a  c:%NEQ a:chess                  ; BNE	CHESS
		
:nogo		cmpr.v  a:%Xw v:#h0D                    ; CMP	#$0D                ; [Enter]
		    brch.a  c:%NEQ a:nomv                   ; BNE	NOMV          	    ; MOVE MAN
		    call.s  a:move                          ; JSR	MOVE          	    ; AS ENTERED
		    brch.a  a:disp                          ; JMP	DISP
:nomv		cmpr.v  a:%Xw v:#h41                    ; CMP   #$41		        ; [Q] ***Added to allow game exit***
		    brch.a  c:%EQL a:done                   ; BEQ   DONE		        ; quit the game, exit back to system.  
		    brch.a  a:input                         ; JMP	INPUT		        ; process move
:done		move.v  d:%GL v:#h00
            brch.o  r:%GL                           ; JMP   $FF00		        ; *** MUST set this to YOUR OS starting address (in this case, zero)

                                                                                ; THE ROUTINE JANUS DIRECTS THE
                                                                                ; ANALYSIS BY DETERMINING WHAT
                                                                                ; SHOULD OCCUR AFTER EACH MOVE
                                                                                ; GENERATED BY GNM

:janus		load.o  r:%GL d:%Xx o:STATE             ; LDX	STATE
		    cmpr.v  a:%Xx v:#h00
		    brch.a  c:%NEG a:nocount                ; BMI	NOCOUNT
		
                                                                                ; THIS ROUTINE COUNTS OCCURRENCES
                                                                                ; IT DEPENDS UPON STATE TO INDEX
                                                                                ; THE CORRECT COUNTERS
		
:counts		load.o  r:%GL d:%Xw o:PIECE             ; LDA	PIECE
		    cmpr.v  a:%Xw v:#h00
		    brch.a  c:%EQL a:over                   ; BEQ	OVER           	    ; IF STATE=8
		    cmpr.v  a:%Xx v:#h08                    ; CPX 	#$08           	    ; DO NOT COUNT
		    brch.a  c:%NEQ a:over                   ; BNE	OVER          	    ; BLK MAX CAP
		    load.o  r:%GL d:%Xz o:BMAXP
		    cmpr.r  a:%Xw b:%Xz                     ; CMP	BMAXP        	    ; MOVES FOR
		    brch.a  c:%EQL a:xrt                    ; BEQ	XRT           	    ; WHITE
 		
:over       move.v  d:%Xz v:MOB
		    addr.r  d:%Xz a:%Xz b:%Xx
            load.o  r:%Xz d:%Yz
            addr.v  d:%Yz a:%Yz v:#h01      
            stor.o  r:%Xz s:%Yz                     ; INC	MOB,X          	    ; MOBILITY
		    cmpr.v  a:%Xw v:#h01                    ; CMP 	#$01           	    ;  + QUEEN
		    brch.a  c:%NEQ a:noq                    ; BNE	NOQ           	    ; FOR TWO
		    move.v  d:%Xz v:MOB
		    addr.r  d:%Xz a:%Xz b:%Xx
            load.o  r:%Xz d:%Yz
            addr.v  d:%Yz a:%Yz v:#h01      
            stor.o  r:%Xz s:%Yz                     ; INC	MOB,X

:noq		cmpr.v  a:%Xz v:#h80                
            brch.a  c:%HOS a:nocap                  ; BVC	NOCAP               ; (since 6502 is 8-bit, manually checks for overflow)
		    move.v  d:%Xy v:#h0F                    ; LDY	#$0F           	    ; CALCULATE
		    load.o  r:%GL d:%Xw o:SQUARE            ; LDA	SQUARE       	    ; POINTS
:eloop		load.o  r:%GL d:%Xz o:BK
            addr.r  d:%Xz a:%Xz b:%Xy       
            cmpr.r  a:%Xw b:%Xz                     ; CMP	BK,Y           	    ; CAPTURED
		    brch.a  c:%EQL a:foun                   ; BEQ	FOUN          	    ; BY THIS
		    subr.v  d:%Xy a:%Xy v:#h01              ; DEY			            ; MOVE
		    cmpr.v  a:%Xy v:#h00            
		    brch.a  c:%POS a:eloop                  ; BPL	ELOOP
:foun		move.v  d:%Xz v:POINTS
            addr.v  d:%Xz a:%Xz v:%Xy
            load.o  r:%Xz d:%Xw                     ; LDA	POINTS,Y
		    move.v  d:%Xz v:MAXC
		    addr.v  d:%Xz a:%Xz b:%Xx
		    load.o  r:%Xz d:%Xz
		    cmpr.r  a:%Xw b:%Xz                     ; CMP	MAXC,X
		    brch.a  c:%LOW a:less                   ; BCC	LESS          	    ; SAVE IF
            move.v  d:%Xz v:PCAP
		    addr.r  d:%Xz a:%Xz b:%Xx
            stor.o  r:%Xz s:%Xy                     ; STY	PCAP,X         	    ; BEST THIS
            move.v  d:%Xz v:MAXC
		    addr.r  d:%Xz a:%Xz b:%Xx
            stor.o  r:%Xz s:%Xy                     ; STA	MAXC,X         	    ; STATE
		
:.less		                                        ; CLC	                    ; (don't need this)
		                                            ; PHP			            ; ADD TO (nor this)
            move.v  d:%Xz v:CC
		    addr.r  d:%Xz a:%Xz b:%Xx
            load.o  r:%Xz d:%Yz
            addr.v  d:%Xw a:%Xw b:%Yz               ; ADC	CC,X           	    ; CAPTURE
		    move.v  d:%Xz v:CC
		    addr.r  d:%Xz a:%Xz b:%Xx
            stor.o  r:%Xz s:%Xw                     ; STA	CC,X           	    ; COUNTS
		                                            ; PLP                       ; (nope)
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
